JKenneson/Smart-Doorbell/Arduino Testing/Camera_Test/base64_640_480_test.txt

/9j//gAAAAAAAAAAAAAAAAAAAAAAAAAAAAAAAAAAAAA=EgtRBFEEAAAAAAAAAAAAAAAAAAAAAAAAAAAAAAAAAAA=BgYNCQoICw8OEBAPDg8PERMYFRESFxIPDxUdFhcZGhs=HBsQFB4gHhsgGBsbGgEFBQUGBgYMBwcMGhIPEhoaGho=GhoaGhoaGhoaGhoaGhoaGhoaGhoaGhoaGhoaGhoaGho=GhoaGhoaGhoaGhoaGhr//gAAAAAAAAAAAAAAAAAAAAA=IQAAAAAAAAAAAAAAAAAAAAAAAAAAAAAAAAAAAAAAAAA=AwQFBgcICQoLAQAAAAAAAAAAAAAAAAAAAAAAAAAAAAA=BgcICQoLEAAAAAAAAAAAAAAAAAAAAAAAAAAAAAAAAAA=MUEGE1FhByJxFDKBkaEII0KxwRVS0fAkM2JyggkKFhc=GBkaJSYnKCkqNDU2Nzg5OkNERUZHSElKU1RVVldYWVo=Y2RlZmdoaWpzdHV2d3h5eoOEhYaHiImKkpOUlZaXmJk=mqKjpKWmp6ipqrKztLW2t7i5usLDxMXGx8jJytLT1NU=1tfY2drh4uPk5ebn6Onq8fLz9PX29/j5+hEAAAAAAAA=AwQHBQQEAAAAAAAAAAAAAAAAAAAAAAAAAAAAAAAAAAA=QpGhscEJIzNS8BVictEKFiQ04SXxFxgZGiYnKCkqNTY=Nzg5OkNERUZHSElKU1RVVldYWVpjZGVmZ2hpanN0dXY=d3h5eoKDhIWGh4iJipKTlJWWl5iZmqKjpKWmp6ipqrI=s7S1tre4ubrCw8TFxsfIycrS09TV1tfY2dri4+Tl5uc=6Onq8vP09fb3+Pn6/90AAAAAAAAAAAAAAAAAAAAAAAA=+SJWKjGDnNMgR2Y/M2fTNcqske29zQRSBgE1aijIILM=YFZ2tqbRJwrzsAW+Ue9VL7XrfTFKRuzy+i5/U9qaV2k=E1Kipxcmcre6td6jIpkkdEwcIGJWqo3dGJ9+/pXRG0c=RniznzSbFXPGS3T06U5c4AY+1DZFzqvC2jtL/pdyCEE=9wHv0rp55GCn52x2xWM5XkWtDB1S/aEY3Ese2a5Z5XY=Yksxbvk5rWCS6E3uaNjCyL5smSdvAAAAAAAAAAAAAAA=6h0Ei4P3jjHWr9kWLglifSlYLs/Rb9ieCRPgqs1wzPI=z6tctuc7jtBUAZ9OD+dfPXxlu5rz4zeNMzO0cN2sSKU=jhcKM4HQVlNfu4j5nzNnp/7K0kn/AAAAAAAAAAAAAAA=iQAAAAAAAAAAAAAAAAAAAAAAAAAAAAAAAAAAAAAAAAA=RlmlG5jyeprmkkq0tC1J8q1PINVLhm+Y5781zk7sDww=30zXTFaOwmyhKW3E5YZ9DVdWbB5YVd0ok3GNKwHenQI=QPazzS34jnRl8qIxuTIO/IBGf0regoTm41NiJuS+Esw=MpkhyzMCoxz3rOhleSRiScDp71jLROxRYDsOCT/jQHM=/CWx7VHNaV2h2HhiAAAAAAAAAAAAAAAAAAAAAAAAAAA=YRyMYY8e9S/IZajlZscn3Oa07aZgMbmxWbYzdsLthj4=ZsexrrNLvXG352HPrWfkDPRvDepuroPNkHphiOtfW/w=LdcGs+FYUdsz2bmGTJySOqn8Qf0oo3VVWCcrxsdlLEk=PE8Uq7o5FKsPUHg18oeItOu/CfivUtLuJp2RJfMgZpA=nfE3Kn/GrxStyyFSb1R7V8IvFEepaGdNu5ib6zkYBpI=Qs0ysS27JOSckj8q9IrTDTUqduqJqXcm31IZ4RMhDdI=uF8S+HpHDNGzlTXFi6Vpc76mtCbXunjviPR5VLks+fU=ya801iwdC2S3Xrmoha+hcm+5xepwuu7lh+Nee6yjtKw=Mt9M10poybfc5e4DjOC31zWbKrZ6n863TW5LZVaN2bA=CcitC0hMa5O7Hf3psETMXzySc+hqHcwxljUxtsMh3Ns=ScsT70xyRjLE57Zp6XHdLQhaVu24k9801Ac5ckn60+o=2K5BcI/LoxyPQ4oilLrwxznH0p2BseWbAAAAAAAAAAA=aT3BCBmxgMaQu2Op/Ol5CejGhsjPzCkz2JY+hzTHcT4=7/Eee1IHOBwcnFHQV29RNzL8pPPY+tNLMQp+bJ9DigQ=AAAAAAAAAAAAAAAAAAAAAAAAAAAAAAAAAAAAAAAAAAA=MwHbtVyG32EHv0rib6I95K5cjgHBbk9KgvNRtdPGblw=MwH3V5NJXeg51FTV2c5qPiW4utyW37iE8fLyT+lYqjM=ln6scknvXRCPKjx6tV1JXZaBO0dhwAakpMxA9MVreH8=RX1m+VMDyVGXY9MUbFJX1PRzDHbxLFGMIowKzZTwcis=DrcswNQsBM/mA4YdKyrexZZ2MoAQVundE6XLUr+WP5U=Q43DLYwSMcUrdiSaIZI9K0rMAAAAAAAAAAAAAAAAAAA=p8AvC0gxm68+dsepmcfyUV8o/EZhN8V/HjnqNbmTP0M=isJz92EfVjS1Z6p+zXKYvHA2dWh2kd8HNfY9aYbeQT4=hz/jZN/hm+z0VQTx718NePY8XUoI5yaxqL99IafunjE=q6gMxP4VzVwME4xWkdBGfIuOn4VWXrhupNbaNq4nsV4=5yGO326UsNuOGkAx1pgtB89yFXyovvHrimQxhEGRyfw=6mWwKxIB09zQDwAAAAAAAAAAAAAAAAAAAAAAAAAAAAA=MrZIweKbvoO1yzF1/CtC3fJAHX6VnJDRr2kuCK6TTp8=kDPHrWbA7bRb3aVwenevoX4K+KV07X1tLh2+zakohAw=8CXjYT+o/GoT5ZJhL4dD6Orx34++HRNpVj4jtY2NzYw=gguCo4MLngn6MRj/AAAAAAAAAAAAAAAAAAAAAAAAAAA=1cZaCKZWdQcHbnqD2r63iZJIkeFt0bqGVs5yD0Nc2F8=jZdToPqKaFZkKuMg11VYKcGjNOzuedeLfDgKs6ICvsI=vE/EOjFC/wAAAAAAAAAAAAAAAAAAAAAAAAAAAAAAAAA=9K6YsyaOUu7QjPHHfFZT2pbgA/hWyJFh0/awZh+lTPE=BQMU79R2Kzr0yOlQyJ3/AAAAAAAAAAAAAAAAAAAAAAA=LSEMYQdB+VIV4Jxx0oirBuhjAAAAAAAAAAAAAAAAAAA=JgQwBFJjkH+lK73YxOnWkwScClfuK3UQjjikwD0HFAA=m0EAAAAAAAAAAAAAAAAAAAAAAAAAAAAAAAAAAAAAAAA=dcCmZ5yMVSKVxDj3pOo60BfU/9H5bitmAyeQBxUNzqk=aWJ+dtzgYAUZzXDGLbsj3J1Y01dnP6h4jubglbf9zH0=9vU1jMQxJfkk5P1rojDlR5VatKo7jguT+NTrGRngdP0=abZkmSgYC7gOBSgDpgdanXcRYtLKa+uFt7dS0kh2jAw=816/pWgx6HYJDH/riuZT75zisqkmvdNI7EdyvBGO9Y8=OMDmoQ7mbMPmNUJmCcEZNbRvbQmxnvlyDnjPJ9KdGOM=jGM0+hN9LFiIeuPbNaNuMQPjHQ4pfZKR+o/7NVr9j+A=X4JixjFiWx9ZHP8AAAAAAAAAAAAAAAAAAAAAAAAAAAA=1hWj78PR/oC3Z7h+zBZifxldz4BEFoWz9eP619bVthk=bhU3RkeKF3eH78HvGP5ivhz4hxYu5uOcmsK2lYcfhPE=LWF+d8iuXuV9uDVx1HsZ8vfOM9gBVXoxzjFbrYlifZw=uwODt9qZcSGFDhQWA4FEXuIrW8LZ8yTqatHkemKmS1s=gNBPGe1OznjaKuMewMkCjAIAAAAAAAAAAAAAAAAAAAA=LDParMYwvHNUMnjJBq5GcHGfpWT3GmaVs/vz71uWMuA=gD8qiwHWaZdbCOn4V6LoGoumxoXKyIQ0ZBxggjFYzTs=aDR9qeF9fh8T6DZapb4Hnp+8QfwOOGH5g/hireq6Xa4=t6bdadqMfmWt1GY5Fzg4Pp6HvXfD3qS9DJ6PQ+PH0y4=dG1K90vUQPtFnM0DHsQDgH6EV9N/C3WTq3hK2jmObiw=T9nkBOTgfdP5Y/KuKhJxqpM0nsdpRXpGRUv7RLqFkYc=XpXj3i/QCjSfLxnpXkYmHJVv3N6TurHjuuaZ5cjfLn8=CvOtX0VZCzR457GrgNq5xt5oYVm3FQPrWNPpscJIAAA=da0u9hIz5ocdPwxVGWPHIFUthFR0IA45z6VXkAAAAAA=pK4NlRgX4XgeuKQR7elX0JGsvBqIjHBHSnFjQ0jHTmo=OVN6lWAppAyohMb7GB9AanIPbpS5ddSb2GEc8Y+lAUg=yR6cUpPuUg56nFN5pWF1A8GkwFPAwT1wKfUdxpHXHHY=6UgXHp+VBBGRliAKQg5PTI7VXkWmNKnApMemOD1p2DQ=sf/S+PdS1G4kQ4YqCOgNc/Ixx0681kkkbVKjm7sYDkA=J9KOpGO9UmzIsRowAAAAAAAAAAAAAAAAAAAAAAAAAAA=vawj1r4feFPsFkNVvo8XM3ESnqo9a6e5jwAAAAAAAAA=pmy7GLcRnHTp1rGuhgnjiiNxaGTNxknmsiZizdOK2TI=bkB3ZGBx65p67j1H0p9CSxCC3BHHStBRttZCAAAAAAA=Vi1a5+r3wTtDY/CTwZCe2lQt/wAAAAAAAAAAAAAAAAA=6mbUZ2zjr85qau8H5f5C6s+k/wAAAAAAAAAAAAAAAAA=hX1LWuH+F+oVN0ZniNd2h3w/6Z/1r4j+IsZF1N6BjXM=4j+N8gj8J4VrQO9jXK3PJJxVR7DuUJenFUX+8PftW60=VcVyRLuRVCLjbnpULDcckZohZLUVw9hijBPTtSba9Bo=FGCQMUAZBPr701zJCbHZ+XnjH6Uoy/pimNjouNy5qeM=OD2xU69g5tCwjfj6VaRj3qGuoXsXYHIwK17WUgioe5Q=dJp1xgZB4rtNEvCjKc45qGB9M/AHxUFnvPD1xIuyfN0=WoPUtgAAAAAAAAAAAAAAAAAAAAAAAAAAAAAAAAAAAAA=W+BHc4tLsAfx4JRj+AI9to9ai+E2t/2ZrP2eRsW9+BE=uD0Dj7p/p+NcU3yVX5M33gj3iivVOcDzXOeJdLW7t2Y=C/MBzXFjY3gpdjSm7SPDfFGjiMvxXlOtaeVZuO/SuSk=yNZHEahaYySK5u8t+ehrZslGNcxEZ4HFZksZA45q72A=M+XEedx/CqTqXOW4HoKtaLQQxkAAAAAAAAAAAAAAAAA=qRxmoWUjrirTBNDT6ED8Kb9cdKa0YMrXMRkTgDIqO3k=WZSrHkU2rIW6JcZGAaaV4qE2lZoLhz14o780PqIYc5E=zxSHJ6Y/GgbQjg7SAAAAAAAAAAAAAAAAAAAAAAAAAAA=AAAAAAAAAAAAAAAAAAAAAAAAAAAAAAAAAAAAAAAAAAA=9KzSSWxyAAAAAAAAAAAAAAAAAAAAAAAAAAAAAAAAAAA=TkUKTnGfpU3urWBPUcBnvXb/AAAAAAAAAAAAAAAAAAA=rQ5Y/wAAAAAAAAAAAAAAAAAAAAAAAAAAAAAAAAAAAAA=2c9K4k9bl7MybuLHTHBrn7tfmz2I71otRdTnr5wTtU8=1rJbg89RW60XmQ0iIAAAAAAAAAAAAAAAAAAAAAAAAAA=WgQfsVx67DjHNE3psUrH66fD5BbfD/wqj4URaNag+2I=Fc1+cmnMZGnk4G+5lbj3cms6v2fQSd22fUP7Kigar4g=SOn2dB/49X09WtD4X6kz3KGtp5mkXig4zEa+KfiUv+k=U+em41zYj+P8i4fCeC62Pnb1rkboHceKuDQWM6TPJGM=8qpS43Y7d62voLQQr0GBx3pMAkDjmndtaAmmIPUEf1o=XHTGMmht7BdAPw/wpc4Ix0+lP3nYQffx2HSnjGcYHak=oPIF+WTnoamWlvqUrJFhDwM1ZjIY8469KiWmxLLcJwQ=HrWlauRzxx3qHuVob1nNtx06V1Wm3Owrjk1m9wPUPAc=rkuiaxYarAf39pKGAzwVPDg+xUkV9sWtzHe2sFzbtug=Z41kjPqpGR+hq8M7TkiZ7IyvFuhjxJ4a1LSz964hIj4=cfOOV/UCvm3SJJLWYq4KzQvtbPBVx/8AAAAAAAAAAAA=/dPpjw7qq6zo9rdg/OV2yezjrWpXZSlzQTMXoFMljEg=hBHWnUjzQaBHl/jLRBuYqvHrivFPEOmbC+F5rx4NnW8=VHnGq2eC2Frk72A5PHWuiLZm0c/dW+0Hisa6AXORWi0=rCb6mY8Jc7n/AAAAAAAAAAAAAAAAAAAAAAAAAAAAAAA=omRsMZJqMrnkD6ii9kBGy+uKjbI4/rVoNHqIy5HOBVM=ni2OGQZPfFFwJVcSIMdfpQeoyP0od9xITFJjAqZPyDQ=EI9MEUgHHApeo2NB6ZXt6U1kzz27e1NO2gtFqIF+Ue4=RmmkbF+bGR+tUmF9SFiXJwMUqxZ+YjJxTuCP/9T4iuc=eGwc4quSB1z6VOyGwVd2CenrjrVhBwoAAAAAAAAAAAA=yOD04p47f07UnJ9BF/RtHuNd1KCws0LPKwAAAAAAAAA=jYWVpoGlW+m2IVY4gN5H8TdzWNd9DSOiuVpZw74Bzmg=ZMqcVy+g0Zt5BkNjp24rlNVxECB1JxWkXsJnJ3OMkDo=45rPPfHU10X01Exq5J6EDtUqgZApp6i2LKDGO9aYQPY=zjHUgfrUVG+UI7n63W5bT/h7ER8rW+igj2Kw/wAAAAA=k0chraNv7xJ+uTU1fshE+pf2VFzqHiNu4hjB/M19N1o=Yf4H6iluVdSXdp12P+mLfyr4q+JqYvJxyRk1y4j+Pbw=i4fCeBa0P3jHHeuRucE/hjFaR2uBmTHsOuaqTYUrkYA=T6VvEQ0gHGQfbimnpjjrVJ+QkKPl6c/h1pOuOevHFTw=+t7AhM9D2zSct9Kq7Bkq4AAAAAAAAAAAAAAAAAAAAAA=644z09aL30GtydOgP5VMh5HGe1Q9QLMTc4weKvwtjqY=pegI2LWbaeOfSuo0yT7rMeazlsM77w/PhlUnjoRX138=BzxANV8LrYStm400+Wf9pGyVP8x+AqabtVQSWh6JXgE=8U9EGheLku7dStrqimY8cecD84H14b/gVb4qLcE10Jo=b1sdX8Ldb8u4l06VsJON8YPTeOv5ivVKWEleDXYJrUI=iuogx9c08Xds3GWHSvD/AAAAAAAAAAAAAAAAAAAAAAA=J5JrVkUZiF4ridStsbsjpW0XcTOWvkIyEGTWJNaHO50=Ru68irvoIzp4+px+VZ8qnJJ6Zq0xdSo6+1QkcHFXuLw=yuQDnnt3ph4GOc+9PURG4B5xz1qLvnGatB0EHfH50xw=BhjAprcOhR2m3kJ6qe/pVgHIz1ov0Q9NxOvTvSfnU60=tSRpxnpzSUXGIwz04pCuCDyeMdKVxNkbYT7vHrUBJkM=znb71aGS7VXAGfqaO3ynIpID/9X4lurlZyeMZqjsLH4=bPB4qblM39D8Lalren6hfadCWstOTfczMQFQY9TWWCo=QGBymMg+tSwRMrbm5XAxn608DPYk+g70rW0Cx7v8OPA=svhzR/tl2o/tK7UN05Rf/r1raoWYHy2OTXJOXNI12Zk=1m9wsv7wHHrXQRZdQDwaliG3NsBGSa4PXIyrMWzntVQ=AZxd1w+c1SAByeM10shihc809eMfWl1DoW48Z4PXrWo=26blgHczxr9csBU1H7o47n62eMwLHwAAAAAAAAAAAAA=YW/wr83dDJGn2mc52Anioqy+FeQon1V+ylk3/iMj7vk=UYJ9819N1th/gfqKe5Xv+LC6/wAAAAAAAAAAAAAAAAA=kn7xrlr/AAAAAAAAAAAAAAAAAAAAAAAAAAAAAAAAAAA=bIHqB61ugEIwByT9Kjx+FVqToGM84Pr1o7VHw7jfkNI=OeacM44/SmnoIcGxnPUGnjpnn8aL3YbICNynBzxToWw=jn6VQ+pYB568Cpl7+lQw6liM9AOKuQPjAxn2qNbXDc0=W0OMFjyTXS6c+CPT1/Kpeo7Hb6NNtZea9++EOv8AAAA=v2xdwILsC3myeME/KfwOPwrFvlkmO10fStcX8UPD39s=3hWd4Fzd2H+kw4HJ2j5gPqM/iBXbWjzU2jODtJHjXh0=1SS0mguLckSIQ64/lX0fp19HqVjb3cLArKgbjse4rkw=I7Ta7l1ehaor0DIZIgdSDXnHjHRtxdgMDrmvNxkbTUg=2ovdHiHiLTfLZ8jivNNWgLMyxg981nBls5a7tPLJ67o=sK7ix25rVdiepj3EdZkydjz9T1qlsJlGRODgniqzDPQ=rRbAQMuecHce1QsOTxTQkM28+1RHoMirTuK4w03bg9Q=+9NXsDRDLFvUgD8KrQ5j+VqE7ICfg55prD+VJu7GhMc=QfhzSEetTdh1E7VFJJt+UHtzTJtrYhCNJzggCptm0DY=jr61TY9gVdx7jHWkwDtIUcfrRcN3qf/W+F2YdOp9KFQ=dtkcClppWCoPUmgpH0R8T5LX4VfCLQPhxo0yNruuqL8=1yRTl44TyqHHTccdew968HjjVVXaMAAAAAAAAAAAAAA=nA4/lXb/AAAAAAAAAAAAAAAAAAAAAAAAAAAAAAAAAAA=+S73Hk444wK7r4H+AAAAAAAAAAAAAAAAAAAAAAAAAAA=M9CTz9Aa5Urlp2d2eceLZU0T4keMNJ05M2Gl6tLZQA8=cRnaf1BrQspDPCsrROoPTiphJTpxmuquG51egeFrjVs=R7vVZFP2OE7VPqa8m8YKIp3A7HjFaQavYTTPPbrqSe0=VTHtXTfQhDlPTinoOf8AAAAAAAAAAAAAAAAAAAAAAAA=3XkPP/AxU1NrFR0aP1W+LF2tj8MfGM7dtGuVHPdomUc=6mvzq0rK2lsp4IjX+Vc9ZWrP0X6ijsfVn7JpDP4n9R4=UOP+BV9MV04f4H6kz3K9/wAAAAAAAAAAAAAAAAAAAAA=/TqcVyYi/t/kXD4TwLWzh2HXNclcdc4x61pB21Bma4w=Hqc9OmapzD5DjrW8RaDVwQOc4FNKjvz0xVdRbCZGeMY=BTDz9KNBihQRyevSgjJHFF09BDuSfen57UkwHDkDjjE=SRjBYZ79BTHuTrg8c+vFTJ0/nUsL6kyNjgfe7GrkGAc=nkk5zUvYXU1bZhleePpXQ2D425PFZXK6WOu0iY5XmvQ=/wAAAAAAAAAAAAAAAAAAAAAAAAAAAAAAAAAAAAAAAAA=z0ccN/j+NbIrtpvmppmT0Z81eJNIPhjxVf6coPkBhNY=5xjKNyB+HSvUPhhrQkim0yQ+s0WffqP6158HyVl9xtI=1hdnotFeoYBWPr1ktxaOWH3RXLi43p37FwdpI8F8Vac=PPLII1xGDgnFeZ6tp4j3BFFcMGdDOI1G3xniuau4euQ=VutTN6GHdR+o5NZM0fOd3NWtw6GfKpxwDmqbpj8KpMQ=QuhIOe9QPySDj2qgVmRdajcL0br6VZPUi/yaTr3qh20=Rp+tVLiL+IfeFCQn3EgfzBgn5hxT8c80mlcBMZ70hGI=k7XDZkUkoXpyf5UxIw3zyUbIG+pNtA6DoKavDHHfmkg=LoUnHb60wHIbg5P86fQSP//X+FkAAAAAAAAAAAAAAAA=FeNsqfQipbZSLd9fT6tfTX1/K893KQZJHOWOMAAAAAA=jCnB446+tTa+gN3Zf07T31K8jtoyQXIyR2Fe0WAh0mw=obS0AAAAAAAAAAAAAAAAAAAAAAAAAAAAAAAAAAAAAAA=WX0/lW97fESM44SK2T73/j7flSpL3rMJyXK2fHGlTy4=uXV9qt4S0+p3s15IW5JMjlufzr2z4VXOoeMNa07wMlk=29zpu7dO8keWjXGWO4c9OetY8vJBQXQcW3qfTHxN8LY=keC/hbNZ6HarBDFIMHqWJB5J/wAAAAAAAAAAAAAAAAA=Nqkoi5r6nAzkn3zUB6+9dT3ErBj1qZQM5xx60tQuWIU=fmGcVu6K4j1bSJD91b+AsP8AAAAAAAAAAAAAAAAAAAA=BbxGuSJtQWOyhwOrO4zn/gIavhe0BQRoTkoAAAAAAAA=diY7H1T+yS4MniZRzxFn9a+nK2w6tF+opblHWZfJ0m8=H9Ij+tfE/wAAAAAAAAAAAAAAAAAAAAAAAAAAAAAAAAA=Vyl0ASRVxGZjg9e/c5qrLyDWqFoQr90YppUnHcZqrMU=ewzl8kfd7UvoAAAAAAAAAAAAAAAAAAAAAAAAAAAAAAA=DD6U4H0B5q7O2hNh6kkcUg4kBwRnvRfQZMD0I6ipFYk=PbP0oAnj4IzV2E+vWs27IZo274OO1bmny8j1qGB1WmQ=3zKfSvQPD10VZBms5bDPpb4Oa6We40yRsJInmxAn+Ic=3gPw5/CvXa6MK26dn0M5/EeX/GfRBLpdprcEZM9lIIo=Ygf8smPU/Rsf99GuA8May+l31tdR8mJwcZ6juPyrlxA=nGo2awd42PouCeO6gjmhbdHIoZT7GpK9GL5opmD0CoY=5gW4jZH+6RzUVoc8HEadnc888W6KiK3lrgHpxXiXiDQ=4o7/AAAAAAAAAAAAAAAAAAAAAAAAAAAAAAAAAAAAAAA=/dxZyew6YrFnhGP1qlfcNzNlTGR2qk6g9OnvWmpN7lQ=YZ/+vULqOuP/AAAAAAAAAAAAAAAAAAAAAAAAAAAAAAA=I8HB9aauVcQjp70wrkYNF7CKTjyJQy/d9qmQhxkdKls=dg8wNQvIW+VPzo1YvUI4QDufJOc4p5UMCOcU9R9ROc8=HajB9Bj2pMQMCRwSD2pu3AJzg9zTuI//0PhlVxjjn2o=lUcf40mUTISTn160qA57nOP6YqNAseh+GLFdMtvPlUc=nyrj1IFbTXpPHr6muebTloaJWRFNqH2eKWV+AilutfY=/ZrL8Mv2JrqWaFVu5tAkZ+cZa8cqrcd9syn8BUyTcJI=W9mFtPmfJfhyy+z2ltCOscaivrf9kTwmIbHXfE9xEPM=Lqb7NAxHRV5b/wAAAAAAAAAAAAAAAAAAAAAAAAAAAAA=AQf8a/OjxXJ5l5JgE80f8vpP+tiFscVOD096hxnPPbo=10OTQCZPGMZ96mjzjk/lRbuOxbhGTzWtYQSXNzY29ug=WnnuY44gOu4sAAAAAAAAAAAAAAAAAAAAAAAAAAAAAAA=ZTIersrLGT+O8mviq3DAqW6kZP1rKorMiGx9SfsjfLc=PihT12xH9TX1DWuGvyainuYviyYQeHr92/uADHfmvio=8d7pbqVj6nFc1XWuy4/CeNayo3NXJ3ScsQAAAAAAAAA=ciqsvuDn17VsiCqvCkDsaa7HkDI96q4BuxnHT0xRvxk=yPpijdB10Gcjk05k2gHPBp27hcTAPT1p456jFD8h9Bw=G7Y4FJJggcYxS2AkDemKmjIyCTzSYrlhSO9WYicAAAA=0NMvQscgtitqzlwVPvSvoPqdNp8vTNdpotzgrzWXTUU=1PYfA+uNp97a3UeC0Dh8HoQOo/Kvqe3nS6ginhOY5UA=6n2IzV4Z2k4hPZMg1TTodX027sLoAxXMTRtxnGR1/Do=18wCObSNTubC6AWe0nMTgex6/Q0sVH3kx09j3H4aa4I=+06SwkYmS3+dM/3D/wAAAAAAAAAAAAAAAAAAAAAAAAA=F1btxyK8R8U6XteQ7ec141SPJVaOmm7wPKtZsdrNwK4=H1G35IxWsNRM5i8h2Zz2rDuYdvQAAAAAAAAAAAAAAAA=fKhyeMVaYWVym646dKgIz1z9KtO+oMhYYyO30qLGeo4=avqTuRMMgZ/AYqM800x6NDSQKb09KatsIgkUOuDySPo=VVV/Iba/SjS4Nj23P0Py44p6xqg4GfelcEKBR69PzqY=7ExOcDI+tNOSPlxTbHa4hbjuRjNNLYAx2GcZoQtbH/8=0fhxVH4dqeOOcdqllDgMjArd0CwWecSzjEaHIGOpqWs=S5R1r3PvnHpVC4vWRsBjnucViorZg2M8+XUXtdPhHmM=31xHbqFHJLMB/Wvv79sS6h8O/CPwp4Rs5XH23Ura2Vc=oHgt0JbP4iOnJKMW15Ib6HzLpMQMbNjnB6V+gHwV0Nc=w/8AAAAAAAAAAAAAAAAAAAAAAAAAAAAAAAAAAAAAAAA=mxUkHDytj0OB/SvgjXpA07Y5BPFTH3qjfmStjlZ/v5M=1qDOWxj8q6OQAAAAAAAAAAAAAAAAAAAAAAAAAAAAAAA=Kah8WPAdtOu+KTWoA6noVDZP8hWUkWnZn6CftLgH4G8=jAHvBEOP+u8dfC8ERwnfgVNb+IRHY+mf2SwI9U8SIOg=0EZ/X/69fUtXh3o0E9zG8U2pvNEuU67Rur478fWvlTw=ox3NclRNV2XH4Tw/W0AY8ZrjrxcMffvWsdRdDKmABz0=jVWTByPWtdQsU8AswGeeuKUjHv25rS3QVhuDggde9Rk=x3J604qyCwh/e/IpOD3B5qZyAioOcd6LaiGfdPA4Bpc=v+NLlD0HDrSMSxKr+tCjZWH1HxgYx6cVMmTihjWmxOs=2x0qzHkfTFR1sJW6l2FuR+datrIMjB6Vm4jsdDp8gBU=ArrdKnIIOajUND0jw3fbHQbuK+o/hhrA1DQfsrsTLZs=BRnupGR/Wik0qqCWx21eFfGjQ/sHiCy1qHPl6gnkzeg=HQAAAAAAAAAAAAAAAAAAAAAAAAAAAAAAAAAAAAAAAAA=j8ua+jVZXVWQgqwyCO4rPCvVxCpvcWiuwgZIoZSDXnM=4u0cHeyjr1rzMarTT7m1F7o8U1/Ttrthelec6ra4Ykc=Sog7Fs5G/gwTwa5+6iGcVqlcnqYdwhycjkVnTqOcnio=1oIounPIPoKqkVaB6kTDHAGcYPSoCo696vpckjfjoM4=TURXjrmmNDT+mKYenHemBDJIEHP61VkiaQbuM9zStZ0=0K9h8BBQDow61KR3od0NaDRxwaABRbsJiEAAAAAAAAA=DBBHHpilYNBCNxKjoMcUm3jr0HUHpTQXSP/S+HQuSOY=nAdxip3LV7Fi2gaeZEQAAAAAAAAAAAAAAAAAAAAAAAA=uQi4LfQVWa5VxhuaTQWPSf2efD7eIvj18PbKJEYRaiY=+kDDjZAhkOf++a+kP209Ye++I3gvQTt8qw02bUOn8Uo=/l8/9+uPxrObSjZ9dvzHdqyPL/C9l9tube1AyZ5FQcc=vX6P6Za/YdMsrU4/cQJHx/sqB/SlR+NhN+6j5S/an1I=ZtfNuzZENuoTPbIyf518V6uRJO/1rOk/efqIwJAM8+k=UIHrXTfXcbT3FCj8anRc4zVXsibFyBF3D0r1v4BW4m8=jL4EDdV1MP09FJ/wrKd2VfRn3J+07N5XwW8Qpx++aCM=5/67If6V8SxJgqv4ZqKyftCY7H0V+y/cC117U1Y4WRE=U/H/AAAAAAAAAAAAAAAAAAAAAAAAAAAAAAAAAAAAAAA=1MMc7jWVf+P8hw+E8A15PnY+9cTdqOcnnpmtExGRMMk=9qpSYJOD9a1SY0yuBtZu2aCPUjA74qxMYUHHP1pmOmc=jNAeo5VSNfkOfwoPJ56HvUuWu49QOMflQAO5qk31JEM=zlVx7mpVXaMDrQNXBMB2B71KOvv0oGToemOmKmjySOY=psIuxMARz0rRgI4CnvWctxpm/ZSdMV0+nzcgg1m2B3M=ol1sKkN1r3n4V6/9h1i38x8RXAEMmTgYPQn8axb5ZJo=KtdH0BXNeP8AAAAAAAAAAAAAAAAAAAAAAAAAAAAAAAA=Cr0akeaDSMYuzufNOkTHCO4+dlG7tz3r6P8AAAAAAAA=gRxzODc2p8txnkr/AAAAAAAAAAAAAAAAAAAAAAAAAAA=uWQubZsjoDXHjYXp3Lpu0keKeJ9L8tnO3pXk2t2YUtw=VxUzeRxGo23Xjv0rmbyHBPSuhMzZz91FgEcen0rKmQA=zVq4XM+ZTyeKqSDr69s1aEyu6jvwKhYDHvTuw6kRA9s=NRMOucdcYrRbghjAEVBK4HA5NO4tiIR7jl+TTtnPBo4=lhFSRTBLkEYqwGDLkc+mKb0Y730AAAAAAAAAAAAAAAA=vU63FqxgXjG4nvTSoLZ4x3ouNan/0/h73Gfwp4A4GD0=aizLN/S7cQJ5rD7w44q3JKMZbIrP3rjuZ89xuds546U=Pt8SODzgVVnYm7PqP9hPQY9X+NOtarOjMNE0bMJxwks=KwT/AAAAAAAAAAAAAAAAAAAAAAAAAAAAAAAAAAAAAAA=IW/WsakbxTfR/pYpyu0vI6L4O6Uup+NdDtpB+7a6UnE=6A5r7470Yf7TCeyPg79o/Vzd+NNYwxKpJsQ5yMLxXy4=ag26RuTg96yw+12DZjucsOv5daYQeOK6rO9wHDqMg+0=xiplOMY70KMg6l23TnA5I617d+zTbi5+OHg1MH5JJ5M=8oXP9Kzm2V0Z9hftUtt+EN6P717bj/x+vjiIZkpVvjI=I7H0T+zDarc6/qbuMi3iVgPfpn9a+p6eHWsmOp0EZd4=Cp7jFfJHxUhxe3BH945rLEL96mOGzPnfXlwz+ma4a9E=luOKqImYswycLnpVRgOlaq7QeZWf/Wccg0YyO4watXs=AAAAAAAAAAAAAAAAAAAAAAAAAAAAAAAAAAAAAAAAAAA=4o68HJpuSxwvShp7MXUcoA4wakHrQk+oIRvvg1MCMYw=02UiVD2/UVPG2OKl3DctRMeOOtaEDckAAAAAAAAAAAA=x65710mnzdMGspbFXOw0q4xtOTXpnhvUWUqFbDY4Poc=tWUkxp6n1X4V1uLxBodteRNucDy5c9Q68H/H8a2a9Ck=vmpoxe58yfEDQv8AAAAAAAAAAAAAAAAAAAAAAAAAAAA=gj6V0Xw018abrsAnk229yphkJ9Typ/OvMbdOW2zNpe8=LQ95or1zAAAAAAAAAAAAAAAAAAAAAAAAAAAAAAAAAAA=u4la8eGmh1vVHnWq2uGbqOa5C+gwW6/TFdS2sZvc5y8=Icbh2rGnjIDccfSrVxdDOlHHQ/hVORc8dCD3FWtBFV0=eSDzUDfXNVqxdSFh65qOTHbg/Sr6jK7yZ4QY96akQX4=Y9aNQTDABHXA9qQrkemaFzK5LIpoww2n86q27lHKOOM=tgd6av1As4z26Uh7+lQ2x2DJA6c9qafx/KhdwCmYCHk=zwOOKauxH//U+HxxgD171esrcyyBmHyg8moZVzZMgRQ=YwRVO4uCchTWcVdjKyszPhsE/Sr1uQvH5cVclZAfdv8=AAAAAAAAAAAAAAAAAAAAAAAAAAAAAAAAAAAAAAAAAAA=tt4o8R+IdfdNr6zrFzeEL0G+Q4A9scVyzi04yXn+aKc=ZSt6fkfSf7NWlfbfGsEzKTHaQtKT6HGBX2FNKsEMk0k=9yNSx+gGauk7RlJkz6H5rfFfUWvdc1CZmLeZMx6+9eI=t78zHr61FHZIb2Mp+vTgn86b0yB26e1dUXfQWg8fw48=1qZAOOaVmtgReteGGfy9697/AAAAAAAAAAAAAAAAAAA=hhWbWqQ76H1T+1jJs+FGP7+qW6/+hH+lfIcH+sAqa3w=Yo7H0v8AAAAAAAAAAAAAAAAAAAAAAAAAAAAAAAAAAAA=T4rxj7ZcYHG41hif4iHDZnzf4gGC57VwV/zkL604vQY=9zHlG3iqjjA46itUwt0Kkn3x39TRwOlVYRGRg5/GmqA=EYNV00ExBwAAAAAAAAAAAAAAAAAAAAAAAAAAAAAAAAA=k9NAuOGQQM/SnA8DpVLYEJJnbkdqfGcgUWH1LEftUqc=HbrU9RJlqPgDNXbd+RzWctSjTtZPmGeg5roLKXkY4z0=amXYfQ6nTrkowyeK7PRL55XRImIGeWrJrQAAAAAAAAA=/aNLzhZV89Mnq/Rse5HP4V67XVhpXhYzn8R5h8bdBa8=vD0Gr26Fp9LkzJgcmJuG/I4+nJrxnTLsowAAAAAAAAA=JiV+8ZpD4T6a8I6z/bugWl0zbpgvlzf74HP9D+Nbdd8=Sd6aZk9worQRha/ZC5t246V4l4n07G/jnPNeJJctRo4=mDvA8p1qzILY5rhtSg+ZsetdEdhHMXsfBPWsK5TB+vs=VcdiTMmUc+1UJV7CrAqyDGMVAyc9BV9LiK7EAAAAAAA=YmVjjIGatAxyRBQexFNx70Ju4Jobimc9jTe4hpAx2Jw=1UuIyPnXgjrQC1HRPvUZ6ipD7Cm03sICMH0NMI561Ho=hewmMd/c+9BI9cH6U7g+x//V+Io0LMFUZyelbUCLBEE=FyWxkn8qzexY2WRVXIxmqO4nr1NJbXE9yxAm0bmNTh8=by33V5zjoactwWp9/wAAAAAAAAAAAAAAAAAAAAAAAAA=blHKzTO8MWPxEfPvXy54WhaCws42+8sa7hjvXJKU3Kw=1pb/AAAAAAAAAAAAAAAAAAAAAAAAAAAAAAAAAAAAAAA=T4N1q7XG5LVgM+/H9apf7vL5il8SPzR8bTebcSnuxLU=eaXbZYgE/wAAAAAAAAAAAAAAAAAAAAAAAAAAAAAAAAA=emRU8KgMMjpVNvUfmaFp8zZxj6ivoD9k+Pd8cdBP9yw=rr/0Uai/vIFsfTX7XDY+F9kOMtrdsOme0lfJcAIcc1M=Vd52COx9Nfsrj/SfEh7hIe31r6TrTD/C/Ume4DrXy38=FlNt7cZ7MayxPxxHDqfNPiIEu4B+tcJfJtyPT9amPYo=ZizALuPXpVNufatugvMqzjoT0B7U3OBx/KmlqG4mMjE=+lNC8Y5x2pt9LBsNAwAAAAAAAAAAAAAAAAAAAAAAAAA=lUBeaV9dh2shQQAAAAAAAAAAAAAAAAAAAAAAAAAAAAA=GMcU1qrhYmXgDnk4GKnQY288gD8KTBK7LEZOcnn8Ktw=P14JqHsUrGjbtnHA49q2bWYIQS1ZvUDoLGVpiOyV22g=kwi2BeBWbWg1uev+CNdfS760uo25hcNjsR0IP4V9SRQ=qTxRyxHKSKGU+oPIrTCu0pRJqdCO9s4tRsrmzugTBcw=TRSAHGVYEH9DXyHNaT6Hqd5p11/rrGZoW99pwD9CMU8=FLZhT6nrvwj19YNRfTZXxHdpujHbzF5/DI/pXs1XhZU=4tdhTVmFFdJBDcRiSNlPQivKfF2nhGkwP0rysXG1W5s=0Xo0eMeIbLazcYrzzVLfDOCKIPQqSOUvoMZ4rnrqE88=bn0raLIsZNxH1/WqEsXUY+lMRSdP5VTlwmeMk9M1onc=Ap7GlJLggelO2ALgj68Vd1cBjKONp74qNlwOBn3FCEM=CMDPb6U0gECn5jsmhjDj39cVGVH50m23ZE7MptmCQ/0=01ZHODT3s0PQXAAAAAAAAAAAAAAAAAAAAAAAAAAAAAA=D1P/1vi+ygwPNcH2q0zYGT0rK5VynJJlvmPtSRLvYsQ=/KD6UnbewXJ5H3EDoBRcvtsLhh18sjNO2g1sfa/xa1Y=utB/ZH+FfhG2jMEWviBL0MMExRHzio/3n2HPoPevF9I=Rhww+orlcpSun/WhT/iSt3PvH9muxNr4NuZT/wAAAAA=0B/xrS/aA1M2fgY2se4SXcwGQey8n+Yoaf1d+oT+M/M=48XTZupMnua8/uicnHrWlO2wmUWwfXNN9cg1aaejAeA=Hjd2qzGcex96d7gjQtMHjjNfQ37JKeZ8bNNPB8vTrg8=5of8az+0vUa2Po/9rrH/AAAAAAAAAAAAAAAAAAAAAAA=x361nN/vJf10FHY+m/2WD/pficZ/gh/9mr6Srow/wfM=JnuKOtfMPxdQ/b7nj+I8Vjivjj8yobM+aPEChXft7+8=XA34GW561MdhmJMvHA/KqTjgitk7qwbFSc/I2Rj2NNA=RsHXkVXUBpI5wTzxSBgAAAAAAAAAAAAAAAAAAAAAAAA=kU1Zg9hQcYwKXOOg4zmlKauFhQRxg07dyR3p2urMWuw=O68imqcSEY5PNCd0NXLKnp6f1qRWz7GkCLKEAAAAAAA=bb+NZsauy5HIBgse3WtG0YuwLZC9hUvsB1GnzBcCur0=LuMFcd/WpaGmeh+H77Y6ZPT1r6j+Getf2p4eW3kbM1k=Hy+TyVPKn+n4VNF2qoUl7tzs6+fvjzov2DxBp2tQoBE=X8JgnKg/6xPusfqpA/4DXTiYpwu+hMHrY4zQdVksriE=uIGKywMHQg9xX1RpOox6tplpfQkbLiJX47EjkfgeKxw=K7TaKqdC5RXcZCEZFch4tsBLCzgc4Oa8/Hx0TNaL948=D/EllhmyOK8w1q3AL4Fc8DWRxWoQ8txn+lc9dx4zmtg=i+piXC4zx1rMmA565HeriD3M+4kCkhBkmqXkE/NJkms=RWRO4jJkHHX61CR6mqvoBG/Q44zTGzzgf1p2Vha3Ijw=+4pvarQ0MY8YFMIx6Z9fWk+63JZDPGJFJHXtUNvIc7U=6hXtqN7XLHPboaRs9v1oTSBiZ700nHQZNHUVz//X+PQ=p5Yxt4HFVyScjnJ7HrWSRpoQMgPGRzTs7Rgfzq0Gwq8=3uec+1b3hbw3J4y8WeGvDNudr61qcNpnHQMwzSkhw3Q=mfbX7bjWsF98MPD2nKscdkt1P5CdI4lSOOP8OGH4V4E=aLbb5UB7t/WuecUpMUJNrU/Qf4FwiD4fWq4wTMxP5Cs=lv2jpNmlWI3Y4bAzWdR/uo27jl8bPgfxTJ/pEvrnFcQ=XB+b3IrWktLhcqNwB7Unse561slfckkUA47j3qeLOe8=ik0M0LXhlwM5r6R/ZAi3fGKJu8emTfqBWdveRR79+10=yY8B6FH/AAAAAAAAAAAAAAAAAAAAAAAAAAAAAAAAAAA=skDUvEoz1hhP6mvpat8P8HzJluA6183/AAAAAAAAAAA=csdx9TWOK+OJVPqfMHiP78hArz3UOpweKURswpm2lsc=4VScHn1FbJdRtlaTlW7moUPyA56mtEkSxe2WHTnOKjI=C+eDtHtQtHcAAAAAAAAAAAAAAAAAAAAAAAAAAAAAAAA=nqKuc5I/+tTk6ZxzTshtsepFMY4Kt6HmlYLlhDng9CY=pV5JPFSxuxMuScA1YEgQLu61D3C9izb8tucZx+la1sw=AevPrSkg8zds5TlccCum0+bG2s2NnbaLd4Zefxr3X4U=HiFbDXYI5mxBdqYXJPAJwV/Xism+WSY7XVj6Brivizo=D/b/AAAAAAAAAAAAAAAAAAAAAAAAAAAAAAAAAAAAAAA=kj5e0695Rx/EAa+hPg1r/wAAAAAAAAAAAAAAAAAAAAA=OPzNcVJ2qJmkttT1KivRMQrN1a3E1swx0rlxkb0rlQc=aSPFPFFjhpOP0ryXW7Xl8iuCnsdMtzhNSg254rmLyPo=gDiulPQzZh3aBTz271g3JMjFIxx3q0gZVMAUZwS1QyI=kjNMRWYYJOOtV3UrVg9yNgRjPeoiNxOOvrVXuJMi4x4=/wAAAAAAAAAAAAAAAAAAAAAAAAAAAAAAAAAAAAAAAAA=U9BE0Um5eeo4p3NJRSE3cTkZoFRYdz//0Pj+Vm7Dr6g=qIjLZGeOKzRTIGON2B8v0qM4PNPQZJEDuAAAAAAAAAA=laKmt/tGeDo7iMyQWCXN6ec4ZYW2E+nzEVM1pZFI9f8=AAAAAAAAAAAAAAAAAAAAAAAAAAAAAAAAAAAAAAAAAAA=RxxxiuW8pXct7v8AAAAAAAAAAAAAAAAAAAAAAAAAAAA=cDP5g15z+03OVs9PjxwYmOfxxRNfuY+oP42fCHiRyZ4=XnvXHXB+Y1tT2EVzz3+mKacjnvWilpqKxICQSD3qZMA=PP1oY0zRtFxivp/9jSLzPitfP18rRXOfq6D+tZ/aQ10=fme0/teH/ilfDKHodWyfwQ18twAAAAAAAAAAAAAAAAA=fSv7LRH9seJRn/l3h/ma+mK3w/wEz3Cvnn4zJ/p1yP8=AAAAAAAAAAAAAAAAAAAAAAAAAAAAAAAAAAAAAAAAAAA=xx071nvkd/rWsReZXPI5zUMfCHPY1onYQw/OcjO3tTk=cYI79DVXE2MOeByaX0wOfWhgmAAAAAAAAAAAAAAAAAA=A7t3xxmnBcgEA9OmaS0H0HDvmkYZQgdaYMkiO5Rzg+s=UyMOM/Tipe4yQvt6cnrip4QQQz8nPp0qQL0R449avwM=kEevFZvcb2Ni0k+6a6Kwm6HNSwZ1ml3PI55r0bw/fsg=VKNhhgqc9D2NZVBo+svCusLr3h+wvwcvJGBJzyHHDfo=jP41sfWu6lLnppmL0Z8Ua9pj+GPFOsaNIGAsrthHu6s=RMdyN+INdT4M8RNoOr2OoKTthlAlCnG6M8MK4JPlZtI=Vz6tVldQyEMrDIIOQRS16cXzJMwCop13oRjqKzrx5qY=0Nbnlvi+xKs5AAAAAAAAAAAAAAAAAAAAAAAAAAAAAAA=vkCAnsK6o6oykc1dxNcscZCVny2wQYA/GrEUZUO48e0=9apSJkkDjuKd0BWcYz7+1V3XPAPFXFisQMM8+9RsMgg=p3BEbJn8O3rUXWqQJoaw9xiowAAAAAAAAAAAAAAAAAA=hAZSMdvSh3ApqTDLgngnnNWxg80OzFsBx2pv41KsO58=/9H4/m3YyelRYOPeslaxUt7EDhghBIxmowKasPQswJg=xk4GOPavrv8AAAAAAAAAAAAAAAAAAAAAAAAAAAAAAAA=8dsbUm0rXKTtdo5v4s6q3iL43+P72UANDqv2EbeAVt0=REPxwtLo9q0zwQxj5pJVXj61ySkpaocFbQ/Rbwzp66U=eHdLs0XaIbZFK+hxz+ua+ff2oLwG6s4FPMdtlh+Jx/M=rSskqcP66EXvJs+HtfbM0hHU9q5OblmPqaunaw2upCU=c9cfSkOcA9O4xVSa7AkSLwAAAAAAAAAAAAAAAAAAAAA=+qf2Kk3fE3X2IHyaCAPYmZKxek0XHZ/M9X/a+fHh/wA=CinvqTn8oz/jXzDB98VE/wAAAAAAAAAAAAAAAAAAAAA=fMbWM/rX07XRh/ha8yJ7hXz/AAAAAAAAAAAAAAAAAAA=6nyn4kwHf+leeX4yx7c9amNimYM65Jz1qm/Ix/Kt0hM=d9CswyDmqoGWbPTrVpK4D+w245pM8duvWjkTF0GnPp4=3SgcYyv0o5Y7XDWw3PPYUDtmnypbAh7fh+NKMnjijlQ=kFtdR46duaUfTrRZXuAkPdeMrUhYnjHNGg9iaJNvJ6k=qzGfXB4rNpAyzGevb3q9DnOetRJDuadu23HpjnFb9jI=jgVDDodPp8+0jHeu20W827eRUPYZ7t8JvFa6dqqWFy4=Ra6kQi88LN/D+fT64r3iurDP3LGU9z5x/aJ8Kmw1rT8=xVbL+4vgtjeAD7sigmNz9VBX22j1rzHTLnDAOeD1Fck=OPvNM2WyaPp/4SeI/wAAAAAAAAAAAAAAAAAAAAAAAAA=P+A13td1F3powluwpG6VcleLQjifF1ruRmPevEvENqM=c/FeLHRs61rFHmGtBULcc+lcbdWjysXlBA9K6otWIaM=Ku4do4HHpWHdQ4yD0q4smxmTxkZ45rPlQ4IHrVLUOpU=nXAwuAaqupHeqja4WIGXkn9KiYU9LgRkd/SoW5J6fhU=atci2owrx/jTCCcYo93YbRGwzyMH6Um0A46H3p+7tcI=1iC5jyhYDkGmW8mRtPXsfWj3baBYmx0FHt2pKwj/0vg=+kHzeg69aiz71kkW0QMccj1yRQPvAt3qmkwLcKfOoA4=lffH/BP7SBpvgLxn4kuMR22oamqeY5/ht0OSfQAAAAA=KSvF/wAAAAAAAAAAAAAAAAAAAAAAAAAAAAAAAAAAAAA=rHwy0g6x4x0CzxgSXSsfwrhUVGCS7Fx+JH6AnrXyN+0=NXgfxHOin7kSAnP+zyPzroxGijExjufG+tyb5W471zc=LkkdjnmrgtCmRNx1GT6mmLwfU1aS2Fq1cehLY4/XrVk=jJ56D1NDXcNDRs/vV9V/sUjHxK8Scf8AAAAAAAAAAAA=e8jToen/AAAAAAAAAAAAAAAAAAAAAAAAAAAAAAAAAAA=hEdj6R/ZaYHxD4iHcWcfP/Aq+n66MP8AAAAAAAAAAAA=/Gsbbub1IH8qxxavKI6btc+TPEuN75Arz2/yGb9aUbU=hswpxy3UVSfC5J6VskBVc5PHAqDGJGHY1QmhSOcYFNw=ZbnAqkgGnjoc560g7fqadrh10HA49KPmalZ3uxAPoM0=KMgdBxTaBDsnHQY9KcOxpIZGGJf5R164qwoAAAAAAAA=gJ1bOB61KnHWoewyyh/XtVuFiMfSpktAuaFvIcg/hW0=Wc3T3PFQ1oUzpLGb5hg811uk3OGXJ6VFk4i6nf6ZcNI=25ETESL80ZU4IYcgg9uRX1xoGo/2voenX5ILXNskj4E=j5iBuH55q8NfnaJmiHxT4ft/FXh3UtGvMCO9gaMOV3c=lt/C4HqrYb8K+Khb3Glahd2F6ALqwuHtpwpyN6HacHs=jiniI2ldLccH7tj1H4U+JhoviyzNxIEs79fs0xPQE/c=D7fNgZ9K+m6eFb96JM1rcKD0rrZBzniSAAAAAAAAAAA=NIyW4LN34rxbcs2vM6Yv3Uec3+k4JeYZf3rlb+2wTwI=t4sRzV5AeeKwruLkjFWtHoIyJ42zjjms2ZM46e4rQRU=HTn69MCqsinPbHrQkDKzjOexqu3SritREbE4wB1/SoQ=r+dUkgGnJFNxxnvTsHUacjjApjAYwB070ct3cnqMbng=wPrVGRTC24AAAAAAAAAAAAAAAAAAAAAAAAAAAAAAAAA=+PnGTzjFREcdOg5rKxp1IJB82cfrQAcqCMAn0przGyw=oeTkfdBJwa/Qr4Jm38E/sO3mrSsyNfaTqN03AyJJWkg=k/8AAAAAAAAAAAAAAAAAAAAAAAAAAAAAAAAAAAAAAAA=6YL34gWLtjFtE0n4gGuWVjSKPs3vXw5+0Rqaz+LNVjQ=bOyVhuHp6VpiXacfmZwPlnVWDSse+etYcowQBnANaQc=oindEDDkHBPtScntz3NU0k9CVsPUYAzwKsx8cD0psdk=WNG06g49K+q/2KBj4keJP+wGp/8AAAAAAAAAAAAAAAA=tiuRbeB1HU3lz/6AlfNMDEPx61nU/isUdj6O/ZYb/io=jxCueDYRn8nr6lroofCxT3A9DXgnxw5u5QAAAAAAAAA=xe8R0+p8meJcl3GenevPr4AsxzUxRRi3BwMms1xk9OM=sK2SsIhdTjke9V2BDqRxnrV2Ad1GfWmYyBkU2r6CfkI=bcY6DNNKkHgHFSlo0PzFOQ2eMGgcduAc0ct9RBjBGe8=T1JOOBg+9Pe9w0Dnjp6803JfgHjFO4A67ApA781YUHA=M4osrD6ksfOOD9amXkdKiVgJoyABnvVuNsYAAAAAAAA=knqMVq2sm0D1FLSweR0NhLjb6jvXUaZOQQMcDrUPqI4=80C7wV3dMivqP4RamL7wmtszAvYzNFjvtPzKf1P5UUc=+Kgnsd7Xy/8AAAAAAAAAAAAAAAAAAAAAAAAAAAAAAAA=nnqc+9b4n4E/Mmna5wFpMWjKA/Nj5T6Hsfzr64+HviQ=Hirwnp98xY3KIILrccnzUAAAAAAAAAAAAAAAAAAAAAA=u4zMXW7Wa9i8qHhe5rzjW9AS1V8Llu5NeJUf7xs6ads=lPMdb08gudvSuC1SzILcd62g+oNHJ31v1rn7uDGfzrQ=eyJZiXcO0ZzzjmsuaIg9OavroFtCg685I61TdD0pisU=eRSMZH0NV2B56n0FWu4PcgYc1C49O3vVxFbUZ7+9MIw=VXUBCPpntTCCeOetS1rdAtRu09zx3qvLH5i+9N73EQU=u21tpHBqySTjjJpNX1FY/9T4+cclTTGHSsUaabFcgMw=SDkdqAcKTz700nsJ22CVmjsLqVfvGMgfU8V+j/xkit8=wR+x7onh6GAxtqFpp2nhc/dkcpLIT9Sj/nUtpp+g5P0=2y7nzBpkYBQDoMCvqj9l/T1fXNTunHzRWwAAAAAAAAA=rXkvU0Wz9D6fZgis7dFBJr87Pi3eibV9Qk675W5/Grw=RrURnA8G1A4cjPQ1jyN8/r9K1gimyJstxg800MMdye8=VNXuiNCRecZ6+tTIP5UWsrDRp2ZIZTxivqv9iYD/AAA=j+J+SSNDQf8AAAAAAAAAAAAAAAAAAAAAAAAAAAAAAAA=+a4X+cexrOp/EYR2Por9ldz/AAAAAAAAAAAAAAAAAAA=X1bW9D4WKe6A9DXgHxwb/TZcDHA/kKxxfxRHT6nyd4k=P9ZJk4+lef3x5JY8d6UNB+ZiTgseRwOlU3HTHANaITs=FeQ81Vk+8h98Vpa6C+g7jp/Kkzjtn8etMBgHIHp6Uow=7j/Op5QE4B7U3jvx7etNRaYk+4Dng5xS7gAAAAAAAAA=uwmPNb0GealAC8D0oV7D2BhlcUsTZUY7cU2m2CZMjAc=IqwhGATz+NTJAyWPk47fyqzGQOlSMuQuM4OPwrRt3HE=/nis2ncLo3bKXlfTiuisJwAAAAAAAAAAAAAAAAAAAAA=4LfW5bCR8R30OUHbenP8s1EdKibG9j3muC+Mnhs+JPA=DqCRKWutPIvrcA/xR5J475QuMepFd9RXgzJbnyZbT5A=jp0YAkelez/AnxMNO8QXej3L/uNUUPASeFlQHI/4Euc=8QK8+LtNM2kk0fRNFemYDWXiub8Qad50bMBXnYynazQ=a0ZWkeReINM2luMdulecaxZYZgRisIPQ2kjib+02luA=81zN5b8t/St47GbMK7hBPQ/WsWeLrj1q13FujNlXLdM=A/lVORQVzgZp2DYqyKB1/Gqjcdc81S2FdELLg4NRnH0=CaoRE4J64PFMK4we9UNNMafboaYeMZH1NO10LQaRlh0=gBUXyn6UraWQbsq3EYRlcVLE4dQc896LNpB1P//V+P0=8cbQPzqPG6sltqWisBnoRx608DIxng9qpjujS0jTX1c=1bR9KgAAAAAAAAAAAAAAAAAAAAAAAAAAAAAAAAAAAAA=OMfZ4iMfT97+grnqw5k2vL8xvRJ+p806SgLjuc19hfs=Mlj5em6rctnezBPbGTWS+NepX2We1+ILhbXQdTmkOFQ=tZOf+AnFfm/8Qrky3UpY5LNVVf43yREfhPIb0hmPrWU=ScMSBmtoA2RFSMHGfWkBx/D+lWl1E9SRO2alTAwB+dI=a1H0NC14PoK+p/2IZt/xN8UoOg0ND/5FX/Gp3mmD20M=tf2xtRD+IPBOnZH7qG5uCM8/NsX/AAAAAAAAAAAAAAA=zqL32Edj6I/ZUlP/AAAAAAAAAAAAAAAAAAAAAAAAAAA=1r54+N0oOoTgfSssX8UQp9T5V8Q/ebJ9zXA3q7yxpIY=Y86gZqhIO38hWsV1EV3AyN3GfSq0oOO3BrRC2QAAAAA=puOevsOOlPW4xNpzkc0m0kAsOc4o0sJ73GnAGPel4Po=E+1HW4MGwozzg9BimKu/G44BPSkFyfOB0P5Uo/Wi1ws=6C4zyelMhwrMPQ0wZYTg4NTLwP5VDB72ZKpC49+tWEM=0x0qLPcd7FqA+vUnHStCBgOD17Um0h7mvaPjkn8K37A=l5GfWolZsOh1ul3GGHNeleFdZk027tL6A/vbWVZVHrg=PQ+2M1nNWdxrVWPsK1uY721guYDmKeNZEJ7gjI/nUtc=oJ80b9zE+K/HmgHwt4z1vThEIYBdNPaxr0ELnKAewHE=WZYarcadc217YNtu7SVZ4TjPzKQRxXnNJaLodEtUfa0=oGrR69omn6nARsu7dJeOgJHI/A5H4Vo16MHeKZzhUM0=EJEII4NZ14c0GNOzueeeJ9I4cgcV5Rr2mAFiRXkwZ1s=2PPdWsipbiuRv7fAPHeuqJkznLuDrkcGsO5h5I5qle8=YRlTRbT/AAAAAAAAAAAAAAAAAAAAAAAAAAAAAAAAAAA=qBkAAAAAAAAAAAAAAAAAAAAAAAAAAAAAAAAAAAAAAAA=Q1gCByR74pmB8veqv2Bsikj3KQ3celVI28mTB6Zwfek=WA//1vj4kYHX86YwwCe1Zalsqg4AAAAAAAAAAAAAAAA=D1X9nLRpNd+P/wAAAAAAAAAAAAAAAAAAAAAAAAAAAAA=fqktz8UPCOksxMFlost4ij+FpZTGT+IiH5VjOas09xs=1sjyDRgPNXP4k19u/s5WBtvARupM+bdXByPQDoP1NZU=NXmkV9hnZfEy6Fp4H1hy20tFtX6kivzi8azmS4csc8k=NFV/vXYiJ5td53H1rLPWtobDe41hmmgg9SKcVLVEipk=7HgVKv3e/NUr21KL9uc/dBwTkkGvpP8AAAAAAAAAAAA=LVv+Ylozxr9UZX/kprK9pajj1+Z0n7XV0ZPi1pMT5Ag=NEVVGP70rkn+n4V4rathh9axTbbv3Yuh9A/srzlPiPc=yZOJNLYc+zKa+x62wz1kKfQB1r5j+MV0ZtQumz1Y/lU=ni/jiOn1PmjXVLyOccVxF6uCRg1MRsxJxycjkVQm68c=6VqugW1KrjB5BOaryj5DWqYre6IOQOPSmlQTmndiW4g=2c5BJ+lMx7GjVWYxcg4wKaXA7damSle4ug0AAAAAAAA=OAAAAAAAAAAAAAAAAAAAAAAAAAAAAAAAAAAAAAAAAAA=qwexYHI5qSPB4PWk7odmTL2/WpozgDHIz60rAWoySRw=dKvQse+c5rN7jNK3fBANb1lIQRzwe1Sw6HTadPgj0rs=XRbo8AgYbg1EldDR9W/BzXf7U8JrZynM+mv5RPqh+ZQ=/wAAAAAAAAAAAAAAAAAAAAAAAAAAAAAAAAAAAAAAAAA=GyyH8Dv59xXhNoPLkGfxrmq/Gy4rQ+lvgBrzXfh+90Y=nYmTTZg8W5v+WUmSAAAAAAAAAAAAAAAAAAAAAAAAAAA=q4jJ1exW5gYY5ryjxJpW1n+X6V49WPJUaOmm7xPLtcs=DDHIrhdRtSGYVpHYGjlb23Kk8dKwbyI46Ecdq28yLak=izxH8KzZ4uPcdaq+oWKMy4x2FU5VIH+TVITIGX5ifU8=NQFSDjvR1FsQkNzjGaa/TjselXqDVyH2JppAPJqgsM4=5HNMKjAz0FOz6CIyBnPaq1zFxvHbg4o1QPU//9f4/bM=2qCVjj/61Yo0tchBG3GOe36VLCp/M8U7iaPpH9iHRZM=Vvj5DfKuU0XSJ5m9vMAj/m1dH+0rqb6p+0J4njeQvHo=bZWdpEc5CgxCRlH/AAAAAAAAAAAAAAAAAAAAAAAAAAA=LudMkGvvv4PWAsPh5pCjrKplP4n/AAAAAAAAAAAAAAA=eb9bLwHIpPzyzqFHrjOa/PXxXM0ly/1pSX72RMdjhLo=+98prNYEFvQGt4DZEV78k570ipjHpVX6CaJBk9KkHoQ=/WjYa2NG2UfKAAAAAAAAAAAAAAAAAAAAAAAAAAAAAAA=I8f+PE/hWbV2kxrr8zuf2xtPx4+8KX2D+90qWEn/AAA=Td/7Ma+f7cEOPWokrTaQo/Ce6fsxS7fitGucb9OlAAA=9/6V9r1eHesvkKfQjmlEMTyN0RSa+XPiRC8088kgIyQ=4FYYp/vUiqfws+fdfjw7+9cFfjLngg04gzDnzjkYFZ8=KD+IrWL0AqsDyOvfNQMMg1ogIozlBS4AAAAAAAAAAAA=RTQOuCKOZ9haXGFsdOvpSBcHJOTRzXQ7D+3pj8aVcn4=npScrLUBR1UAAAAAAAAAAAAAAAAAAAAAAAAAAAAAAAA=0+gE68gVKgGRg80mGtiVT+AHapYzg9BUMEi0hx61biY=IxUvuM0rd+gFbNlJ056cVEh2OispcEGus0i4II6/Sp0=0CPc/gx4lGk+JorWWULb6oogdSeDIPuEe/UfjX0pW+E=fha8yJ7mP4r0GPxR4a1XR5dg+22zxozjIR8fI34Ng/g=V8RW6SxfJdKy3ERMcynqGU4P61NdJTT7lQbtY9F+GHg=h/4R7xdp11JJttrhvstxk4G1+hP0OD+FfWFVhno0TPc=Ciukga6hlrjPEumAq5A6815mNjaSkbUXrY8f8Qacw3c=y/pXnOq2Zy3FZwehozjtQgwTgVzV5D161t2IZh3EPJM=3rInjPOPwqtw6FCVPmOR+NVHQ4GaYio6/h9ahZfUcGo=+lwZXP0qIg4AAAAAAAAAAAAAAAAAAAAAAAAAAAAAAAA=2nPXPtTu77EvYTBA5wMfrURXPB5z2xSemg0f/9D46kk=FQogOXZsAVcngDFYuS2O1ZWNG9SvJpl0trJcqjNBGBs=3C8LngZNQxjaAAAAAAAAAAAAAAAAAAAAAAAAAAAAAAA=0s8+7s7/AAAAAAAAAAAAAAAAAAAAAAAAAAAAAAAAAAA=9q/oKwqTWkO9/wAAAAAAAAAAAAAAAAAAAAAAAAAAAAA=PsXhLR4B/DbKfz5/rU0U3VuVP4PmeQftO6oItJ0uxU4=GYtK306D+VfDXiBiZWJPJpc15truRHY4254bGPx9azQ=nIrohsD3I2xuGevY0gJLEHtTaYO3UevUYzU6LkEcfiI=gFY0rRMsM96+s/2I7Yf8Jx4unK4ZdLhQH2L5/pUJ+8g=JWtodf8AAAAAAAAAAAAAAAAAAAAAAAAAAAAAAAAAAAA=LY9b/Z9nFt8VNJcsVDROuR3GORX3JI8odfKRXQ9TuwQ=cj8+M1nTlKM3YdT4URiNpbqXzTmBQFCHoT1zXg/xWsA=w3E+Vxknis60bTUn1uKlezTPmXxJEQ7jvzXnepJhjg8=etYoowLgcnPcd6zZiQOD9a0irgVXyQPaoWHXd274rS4=SivHwCMjr0p2SBgevFVuNDOhx2+lRM56Dqe+KQbO4Bc=aM9z3NOzzjjNHK3cVwJI4/PpSjsAAAAAAAAAAAAAAAA=elICcnOAapJtCViTOTxggUjgshz1x6UWdxjoWygz6VM=KT0HX6UmmCa6ki9+e+alVjx1pNAtCzGTnPTFWY2wQc8=J5xUMehfhc5HP6Vr20vPooqWuwG/Yy4K810VneCEjnI=ewFZgztvD00pmt7kuyyW8iyxbTghlORX2zomqRa3o9g=6jbkFLqFZOOxI5H4HI/CtcPdSaImi/Xyd8ZfD40D4gU=+8CBLbU0F7GFyfmY4kz7lwT+NXiFomOm90clZMWUqpw=HsfQ9q+vvA2uf8JF4T0u/diZnhCTZbJ3r8rE/UjP41g=0JWqW7hNM6Ciu4zCqGo2onhZSM1y4uHNTuVB2kmeU+I=bS9rSYFeU63Y4LdzXBBnVJHC6nb7RXKX0GCfSuiOqMk=mBdwYz61j3MWCe4HtT8gWplzoc47HmqUq5z2IqraiKo=6ke2faqrD35q0tAuQSDIzUDe54+lPfQSGvzwfzqBhgk=rRaCu9hD1pmPU5poT0RGcjgnjtTGI2/MeBRYptH/0fg=ysz9p1CMso+U559PatuVhDDLLtxIYyFNY9Sn3OltJII=LwXq9g0YZ7iJCpP8O2uEt1PloGC52jvnNKPUZ9j/AAA=Jq9z4Z+H3xt1+1iBlsbZLuJm5UvDBOwB9ecV4N4dQLo=dbN3lHnMfdjuz+tczac3Ht+v/DGlrO39bHp3giHztTs=dMZy4r9HNITy9J09P7ttGP8AAAAAAAAAAAAAAAAAAAA=rqLXPiEwB90VvCEAAAAAAAAAAAAAAAAAAAAAAAAAAAA=ssxrOPTp1NdURN9CM5AIAAAAAAAAAAAAAAAAAAAAAAA=B9c80nsO2hqWYwymvrz9idNvinxgef8AAAAAAAAAAAA=76G/hZ1P7ZK8+AmwOLi7GT7pHXzIqjzOKip8bFHY9E8=hFcpY+PtIuHO1RuGfwr7u0qWWbT4JZlCF0BVfRccZqY=n/FVhy+FF6vJ/i5Ykx+aMfOtVjFZRYqe58meKoNssnE=3rzPVE+bjHtWaexRzNyDuPA/Gs6YdfU1tF2DoVCOMmo=uw459avqSrXK44dhjr7etOzxVWSC1yBmZsBRQFxwB1o=HbYFsL3woH4ikHQmhP3QF6Y4BpVB9M4odm9QHZOcY4o=VeScYwOtF2txpC/QD3xSjnAxTuDGw5BZSKsDGAe9J6A=lqSKcjOOalU88D2qWhk65O3H41ajYgLge1T0DQuwOcg=xWlbtlge1Rsxo1re7IYJEMt7dq6PS1wwZ+XPr2qdGGw=d5odxsZe3SvqP4I6z9r0C60uRsvYzbogW/5ZvyAPoc8=50U3aomxT+E9Qryn49+H21Pwrb6rArNNpE/mNg/8snE=tfj/AAAAAAAAAAAAAAAAAAAAAAAAAAAAAAAAAAAAAAA=aVyEuF+0QKem9cB8e5GD/wAAAAAAAAAAAAAAAAAAAAA=NZcipnHmi0Bx/ifTQyMyjk81474h08qXyK8ZaOx1p3g=3POdXsz8/FcXfQYz610QZm0c7dRdsViXURGeBWitewE=kzx4qhIuc4Ap+oFKUYBOOveqrrydo4HaqQrFZ+BkAcU=QuOTnuarqJJEZHrioX+bp3qkK+pH7kU1jxx+VU0BBLI=he3NVwJJjhxwaG7bhbQ//9L5HurFLKR7yEM0bL8ox3M=2rcv7Qx6JbSXVsqq65znJ5Nczlt3Li9C9qto1n4Rkv8=AAAAAAAAAAAAAAAAAAAAAAAAAAAAAAAAAAAAAAAAAAA=Ig8I/sM+JNUuCBLrul6pdyELggyB4Ixnv91T/wAAAAA=tDtzDYWceCdsCDn/AAAAAAAAAAAAAAAAAAAAAAAAAAA=WbTAyd4GPav0PsABY2oXGBCuMfQVvR+N+hNTZHyF8eQ=H+3r8v8AAAAAAAAAAAAAAAAAAAAAAAAAAAAAAAAAAAA=yJI269ASe9IowcnOaLLRIW5MmDjnip4R6Doab2Ksa9g=4LL+lfXv7FGB4k8YDHJsrc/+PNWa+NCd+U6r9sYZj8A=uOP9KuhnH+wlfMar83as6q99hHY774VRK/xB8Oo4yHk=yMH6V9+qNqqPQAU6C/e/Ic/hQtcJ8T7bztHjbGcEg1c=i17iJp/EfIXjCDbNICO5ryjVo8M2BzXPB6GjVzlboc8=ArLmwM8cVsldiKbY6dahIAPzAYPtVi2K+P3mMdRUZbc=NgH5e59aqTvpYQoQL1FJxnGPf3FO17MEICMk45NNx68=FHLq2wTHAZ6cmgcdfy9al76oGKBk84wOKXaB05xVRus=oA5e+Kd2poCP7succGrOM9MUncaHKckdAR7VMOMYPNQ=tdg20JlIIGeo6VYjJHA7ml5WAuRuFHPQcmrMczTELGM=C9ziocQ2N2wVYhgcepNdNZSYIwfoai2o2dfpE+GXB4o=9v8AAAAAAAAAAAAAAAAAAAAAAAAAAAAAAAAAAAAAAAA=VqvqFjDqlhd2N2Cbe6heGUA4JVgQf0Nei1dGJ8WXemw=ujX11pt1/wAAAAAAAAAAAAAAAAAAAAAAAAAAAAAAAAA=M4yh4YflmvLe2p0Pex9ZwzJcQxzQsGikUOjDuCMg0+s=1E7q5zhRTAz9TthPA49q8m8SadhnGOa8etHlqs6aTvE=PLNbs8bjXC6lbDkY96uOoNHKXsOCcA5rDuIcg5Fa9bk=BjXMWM5GKy5kGOfWn0DrcpOMfw5qnIgwc4zirsLqVmE=kc1WYcHgYHpVWSAjI71G3yg4AAAAAAAAAAAAAAAAAAA=1TfQNtRiw55bipAoBxxg9KOVPRiP/9P5L0/UoR8rcDE=8yt0NdNq2orqWmWaW67zEQNqjtmueUfeQ46I6W60htU=vA13oEUSm+i2Xi7zgouev415NrVnLpaXkMoIlijyeOA=56VNKWrNHa5+jfxKsIPCH7E0Gl2rCNpNEsIo1PBaSWQ=idwP++nP4V8l2MO0IOwUCpq6W9EU3ecmtrnqvwytzJ4=ILJFBLNIAoHUnP8AAAAAAAAAAAAAAAAAAAAAAAAAAAA=Z/Cj5A+P7BvEmoY/hdgR+Oa+WNcOZWIx61hS1ihtanI=F19PxqgW2qMiuxbCstiPHILdT+FLt5z0PSqWm5JKvX0=asRgd/X0pN3Wg7aaGtaHcw45NfXf7E//AAAAAAAAAAA=/wAAAAAAAAAAAAAAAAAAAAAAAAAAAAAAAAAAAAAAAAA=R2myY7HonwiAHxK8JjsbzB/EV97nrTofxH6BPZCVzPg=6h83QnJ/hatMV/CZMPiPj3xtD+/k4ryLWEzuOK5YPRE=rLc4+8GCeKyZlzkdvpW0X1EU2XBqvIMZ3ED0ya0iyXs=lST53UdvWnnA6DFW0+g7ojbnn1pOV6AY/nTTQtxOgGQ=UUNtIOodOg70YB60lrqgewoJAAAAAAAAAAAAAAAAAAA=OGMlSOPanCnYatYZKMYPcVMOQKGHUkQ8EetSKCMZ5qU=7gSqCfr9anEgRfmH4DrSvcHYliVpceYPlHata2Pl7QM=6VDH0Ne1kJbHauhsXwFrOVgOq0qXlfSvRvD9wwK+W2E=wQVPoR0qJjR9d+H9UXWtFsb9DkzRAvxj5hw36g1pV3U=N3gmZNWZ84/HjQG0/wAAAAAAAAAAAAAAAAAAAAAAAAA=ea87sHw20nqMGuGppJo2WqPpr4U61/avhWK3kbM+nt8=Z2yeSvVT+XH4V3FdlGV6abMXuFFaiGSKGUg1w/iXTgU=XYDpXm4xKM1I2o9UeQ+ILHbv+npXnWqWvUY/SsoM0aM=jr2A5OK566h25rfdGbMW6iyTWNPHgHrxTiBRkHBPGao=UgxkgcdKoSKrocnFV3XgirvYGiBxUDvtBz1Iql2FuVE=2eY4XpSrHtHv3NWmLQd0qMjeeMcVSBn/1PiRZGJwMj0=xWnZanNaSL9lkaNlPBHFZWvoTdo9d8A/Em1i1SZvEcQ=nn3VuLf7WegAAAAAAAAAAAAAAAAAAAAAAAAAAAAAAAA=gCuiqSRxk5bj2Nc8lybm8fetY+zf2zFh034Q+HdKtCE=IpNftLeNM8+Wkcp/IbR+lfJdgmW5FKo25tdgj8J75+w=+6Mb/wAAAAAAAAAAAAAAAAAAAAAAAAAAAAAAAAAAAAA=6sAeBMelfMGtsPMc+p6Vy0vhRTZyd03DHPT9Kzy2SM8=4cV3RXYgaQWP16U5Dgev0oTTdgdySM8AAAAAAAAAAAA=J6bDvoatljcue1fXX7FBA8VeL1H/AAAAAAAAAAAAAAA=y/bDA+y+CCe15cDH/AFr5iX7/TIrOpbnYR2PQfhSxT4=JHhEjr/aca4+tfe561eHXvsdTZBWP4oiE2iXQPYAAAA=lekyIfEj4/8AAAAAAAAAAAAAAAAAAAAAAAAAAAAAAAA=1kyA4IOa1FYozMOc1TfLjJ4HatY7EkEg2lSQOuKd94A=PPNXoDEz2PemZBPOQAKlJhcb2B96TOKveNxIXORkmjE=n65xUxulYd+4oY7evFKOF68ZFCdxMUdj3xzTgTgZoWk=oGwSDKe/tSwklMtRuhq5Kp6etSqT+vNJgOM+04Tlv5U=TRJk7pCSevIqGg1uXomAxnt0q/C3OffqKUtGPXqats8=tPPrW9Yv03Vm9gOo0yQAAAAAAAAAAAAAAAAAAAAAAAA=P0+8052y0T+fGP8AAAAAAAAAAAAAAAAAAAAAAAAAAAA=X/AeoiEZubDF7B82AAAAAAAAAAAAAAAAAAAAAAAAAAA=jXXv7FQ2PW/hFrv9neIFtXci31BfKZT03gZU/XqPxr0=+rTCv3WhTWoUV0kBWTrFsJoDkdK48bG8Ll03aSPI/Es=pxUupFeX6xZEMT+dcUGdEkcPqFuVbBFczfRZJNdCe5k=swLqMDgjisW6Q5PBzmqi0LoZsyEn9DVGRQ3I61WtgRU=HHfp/Sqrj8qoRTmlVCQOT2qv5bSNls81qtBDymwYA6g=60wjGMGhagRnJpuenrVbCP/V+HYskjuSfzqxErjBz90=PWpk0iGjTt5OhOD6g45/zivoP4B/GjT/AAAAAAAAAAA=dvqvgOecfZ3uEDPpszMCHDdQmR2IIyfWs5q60Vy4Sac=ufQn7cN3vuPhxYo+Q9zeXDqORhUjAAAAAAAAAAAAAAA=pnrWNXSbuaw2Pq39mbSjHq+o3E8TI0dqNhZcZBI5/nU=9LjrV4e3I2gq7o+GvjVdefr1+WOQZG/nXzhrT/vXHvU=zUvhGcrdZOSCAAAAAAAAAAAAAAAAAAAAAAAAAAAAAAA=25qwmRg9qT2KVjWsuv619a/sTsT4y8YAAAAAAAAAAAA=x+JClsd5+2Cv/Eu8GNxgX04OfdBXy+mRJ7elZVH78hw=djvPhowj+IPg9/8AAAAAAAAAAAAAAAAAAAAAAAAAAAA=q7XGcp0/Gtq6vSkZx3R8j+P4cXM3Hc14lrifM3fvXDA=fumzVjiL9Mlqw7pioJPbpXRHUm9jNZS7bmqJx6fpWiY=tg6FabJXPoc0ZOB3pvTUS3EPXAxk9KYc47HPNUtAY0c=Axz9aTDelSndWDYAAAAAAAAAAAAAAAAAAAAAAAAAAAA=2rAeoPY8ULz1z75pabiH+wNMh+UsnpSug2ZN7mguWOE=B+NBWxPEgTB6n1qzET6cZqW1uK5ajPTpjPersHGOuBg=FRcpmlAxFbdm+NuT1qHsHU6fTpMECu10abBX0qHsCPY=n4Z6z/Z2u2MjNiORvIlycDDcZP0ODX0VW2Gbs0RNaiM=IsiskihkYYZSMgj0NfHXiXQ38MeI9S0eTdi1nPlEkHM=E3zIePVSKeIWzHT6k+k30tnNFcW7lZoJFkQqeQQc19Y=OjanFrOlWeoQEFLmIPx2Pcfgcj8KjDu0n5hUexeorsM=MKimTepHrWVePNTaGtGcB4o075iSo6V5Frtnjfxg15M=T03Ot6nnuqW+Scj2rkr+HGeB7V0R0Znuc7eRHnNYl1E=YyT26e1WtCTHmjIJqjInBz06Yqk0wehRlAU9sY71mzQ=jP8AAAAAAAAAAAAAAAAAAAAAAAAAAAAAAAAAAAAAAAA=U0xaEZHoKb09qaEz/9b4cVsAAAAAAAAAAAAAAAAAAAA=v277uCQMcCtIRJKrRuFZWGGUjrUN9RNWPQ/D3jm6uLU=stB8TXU9zp9pH5OmSzSFzZLxiNc9I+Bx2rs4LVyohx8=MXUH6bhn9K56jbd2a0rJcqWh+lXhvUdJ1bSLW58PSxQ=1kkYhjaPnaFA+U+mOOK1h1rpi17O6E731PgT4sXO/VY=8IOQZG/Dk18/6s4Z35FcVJWijR6nN3B+UjHPbiqjjjo=V1KxL0GfwY4pVI4wMnFU7XFYmQccdKnjGR/wIUh9DUs=M72AUYXvX1t+xSwHjbxYoAwdLhI/B8f1qIr3lcb+E9A=v2wFzo3hA56ajIP/AAAAAAAAAAAAAAAAAAAAAAAAAAA=hmXp5eqQN/49X6DnrWlD436DnshKhu132s6+sZA/Kto=t/Cl6Ga3PlL4iwbbifgdTXg2uxks3pXBS+E3lucHqJA=pOOvpXPzLyCxye1dMSGilJywxioJRlW469xT2QFaUZQ=OBximLgxjp+NadBXQhUE80gHTPPtTfYQznHPejOcZGI=iy2GGeM8Y9KQelQoq9wFA+nqKBnJAAAAAAAAAAAAAAA=6U5TkdKXUkcMA8AVEx8uTOOCKNBjwDIPm4X0qygCjpQ=mPVk6nByRkVNGMjjrUOwWLCcY+U4q5CR0xxUNOwzRtw=4xxWzaOOORStdB1OhsXIK5xXYaVMMqamS0Gj0rw7c/c=cNjOMHNfU3hzU/7X0OxvCfnkiHmc/wAAAAAAAAAAAAA=maleCfH7QRb6npeuwqQLpDaTkJwGXlCT6kEj6LW9dXg=Cpu0jyu0l2SfjzX0F8GdbFzo9zpMrEyWchkh5z+7bsM=6Nn865KOlRFT2PTaK9EyCkIyKTV0Bha/aiW3Ykc4rx8=8Q2PzSYzmvGkuWbR1Q1gjzPV7XDHjrXF38GC2RW0WSw=5i8hOTWFdRjJ9q1J6mNPH1GOprIu3WMknk9gKaAypFk=Lg5IwDSeQqdBV3FbUhYDHNQlCD0607aaC2IiMjnqaic=XPTH1q0xbO5FjjimkZBzj8KpBY//1/hoLjvyaeASoUc=P40rkpW0LsIdFUncARjp3q/BcGMjgjocVD1HsbNreJI=BRKoA9fSvV/h/q7Xgi067YPcRnMMuf8AAAAAAAAAAAA=LlQep9zfs3aY0Hh/U759wE84RRn5flzk49eRzXst9J4=TY3Un9yFm/IGlG6w8n6lz+M/Pj4lTiS/uiv3d7Yrw7U=ZwGOPrUUlorjOcuGyOeuOxqu5IxiulEsZxxkZp4J9OM=0qmhWJBz05qZCW47ZGanzKNWz4Ze1fV/7FcmfiF4pTM=/wAAAAAAAAAAAAAAAAAAAAAAAAAAAAAAAAAAAAAAAAA=4esZ6VGEdjpfDr+VrWjSdk1CEn2+cV+iZ61dD+I/QJ4=yEprjKkeoNdFRXgyFufMfxMt9t1Nkdya+efEWFLgda8=OpbG8jz2/j+Ys3Of0rDm+nX0roTJM2Xgg4+tV3OB9a0=ULUgcZzzz7VFCdy5I5qugrA2QKaCcnB49qoNhh68UpY=x6n1pX12DoJ1wBSdRwOO9DfQAAAAAAAAAAAAAAAAAAA=gdKcvPP4DNAWEeUrwOT2GKaQwIZ+e2KLCZZX7tPU5yA=4GaTGTg55qRO1TsFy0hORx+FW48YXaeKl7jL1s+SDWs=WjdCDUuwHRWL4AzxXVabLtK+gqH2A77QbnayjtxX0b8=CfVBLZXensRlCJo/904B/XH51NOVqqCSuj0auT+JWgg=8ReC9TtlUG4hjNxATnh0GeMdyMj8a7px5otERdmmfKk=C2drkYLcmvQfh1rn9h+JLCd2xDK32ebJ4Ctxk/Q4NeY=qTTTNZLRn0tRXqGAUUAV7qETRMp715f4msMO+0eteVg=mKVVm9J6Hlmt2nLYH6VwOp22CcjpRHYbWpyd/ARk4rk=68hxmtuhPU5q+ly22JdxPXiso2ZyXl59q0WnQWpC6YE=hQOPfrVRkwMGiw9WV5ME5Aqu69cH9atCZCwz0qI5ycg=yDTTuBE2ByBke9Rt0wapAf/Q+F0lXPP/AAAAAAAAAAA=MCpbEWBcHvz6Vcgug3Dg4HQ0pOyElqaNtONwwSABXQY=k6hJayK9tMY5kbcjjqp9s1Etg6n6V/steO9M8ZfDpYY=0kVNWsJiuoWxOGRj0fH91scH2Newa85TRNRZev2d/wA=kah/7u/Rmsnedz89viRKi3U4XG3ccYrxDUnzI3NZUk4=xTMOcjqPWoHyeBz710a2JvqM5HP5U4ntggdau90h21E=4yT8vTODVlMAAAAAAAAAAAAAAAAAAAAAAAAAAAAAAAA=MH5tCU/lMtR9tBLY9e/a9iz4J8Py/wAAAAAAAAAAAAA=yapw4z61hN/vGOOxuWL+VLaSAn5LmNv/AAAAAAAAAAA=0PjfoKeyCjuK6ZK6ZmfN/wAAAAAAAAAAAAAAAAAAAAA=5zXmUtjeR59qH3yOmK5+55P4V0K6EjOkx3JzVZ+Qc/w=qtO+or6kBJJ96roeWHbPHFaXAfnjjr24phGO+PwpNvY=QDTz0zx2NBGCO9O9rWEvMb1J657UDdngflSTdx+QuMc=86QE9BTUm9BLuLk0xnLEBeKG1e4EkcQRiccnqae3MZ4=OlF1ewaj4m+ValXjINA0SgYwalU4IOfyqG9QLKEZ+h4=atRMe3WlLUNC9BxgnvWpbP8AAAAAAAAAAAAAAAAAAAA=0xUtiO20Wchl+tez/DvWRpurWUzsBGzeVIT0Ctxz9Dg=NZNtSTRT2PoGgV6e5gfJPjrRP+Ed8Y6xYIoWETme3AA=Qojk+YAf7ucfhVPT5M8ZwT0Poex/OvLlFK6RundXZ9Q=3g3WDr3hjTb5yTK8IWXJyd6/KxP1Iz+NblehSkpQTRg=PzCitAEYZFcn4jsAAAAAAAAAAAAAAAAAAAAAAAAAAAA=XnGrW2C/HeueLNmcTqmyMHcT7CuOvRJc5CcL3ro2Rkw=zHslhB7n3rOniGeh5qubsHmZsqnnjmqEqZOR2qkxXVw=ryLweOf51WkHXjp0FUnqDICp5HU1C4wMAU47iehG2cE=B9euKiIBODWiY3tof//R+DhjBz+FKGYAAAAAAAAAAAA=UHsffvUySMuMHqeam2pKl0L1vNkhgMevFaNvcspDFic=PTmpa0KbPQ/hj8Tdc+GHie38R+FJgLhPluLeQny7uLs=xP3K9+OQcEciv0l8M/GPw/8AAAAAAAAAAAAAAAAAAAA=l4mtn7gjuvXDdGA+oGVSS9k0bx96F+q/I+KPiJcb7uY=5xz0rx6+IZsn8azpAZEvSomycHFbu1tSeog2nrSE5wA=UtdEg1JkAAAAAAAAAAAAAAAAAAAAAAAAAAAAAAAAAAA=OToI/wAAAAAAAAAAAAAAAAAAAAAAAAAAAAAAAAAAAAA=uN/vWdRe+yYvQ1Y2xATnAAAAAAAAAAAAAAAAAAAAAAA=/MA1dFe+/QJ7IsUdK6XsZnz/AAAAAAAAAAAAAAAAAAA=eGf+VeZT0RvJnnWpLgnufWuanwAAAAAAAAAAAAAAAAA=0qrJg5GatbiuQN3PrUHCyMB3rRbgL1IppYEdKaRIwtk=IP6Un86aQIB16cUg680muqGKOevHvSMVXOT9PenZC1E=hLO2c4Xr9akUBcYFKKHfUeMBhjr709SPw/nQl1FqxIA=4yPSp1PbNJjT6kinHtz0qYds0g2J0I49+tWY2ApWGi4=xPk4zWpAe3fvUPTQbNqycDbk+ldJYy4IPUGoluI6/SY=fBXGa9L8O3OSuT3/AAAAAAAAAAAAAAAAAAAAAAAAAAA=ydw4Ofyz+Nald9N3gmYtWZ4n8ftEwdH12PgAAAAAAAA=lo+PqHz9RXj1m22QZ9a4qqaqM0j8J7f8F9Yw97pLsAg=yi4hBPfgMB+h/CvXq6cO/cInuFFbkhVDUrcSwP6gVy4=LjencqDtJHlXiSwCmQ4wO5ryDxDKqMyQgM3SuGnqdMs=TU4K9015Czz/AAAAAAAAAAAAAAAAAAAAAAAAAAAAAAA=lPvflVRJMudRzjHNZ7LyeOveri+o2VHTOeKryrz/AAA=VLcRWcDPXnH51ARVoVmRuMYUZxiom4OBVID/0vg30pw=oOQR64qiSbYTtAI7EjFTIVBIHY45qHsFkWI3C4B79R4=9WoJtgGOf/1UeQzTtLjZtyMZHWu48D+LtS8G6vHq2hQ=5ilIMcycBZk/uvxyKxnG6sVGVndHceKtYi16L7faDak=Ny6A/cY9R9PSvNL1sscnvUQVi9LmXLhiPrURHPB61ro=9guA+uKUDHA+vSkm29g1JU6jI5xViMZAUHvmm2Jo0rU=P619TfsVMB8UtfycbtBwvv8AAAAAAAAAAAAAAAAAAAA=4YWLYB2a5bNj/gMlfH4++PXNRWfvmcVoaQz9jlx1C58=1Ffon4bk83w7o8n9+yhb80FXS+P5BJaGnQelbvYg8Y8=i/bjz5W9V/oK+WPEyYd/rXmQVtDd6o801RTvI965m6U=3EYxz1H5V0pk2M6VTnI69Kqtzn+tWCIWBI5x1qs3EwM=61SBhg9+opApBI7VSbEMIwemB6Uhz2ou+g+ouOnHNIA=nrn9KV2gt0GM2AQBk46UxYy2DJ26Cm3fYS0JQvHXHtQ=77pP6UN62D0F2nHPGeetP64wOn6UeYWuIG2y8fdPtVg=Wk9BokHzHPPXrUqZA5wcnvSYE6HkAAAAAAAAAAAAAAA=BGfWtO2bkZPtUPYNzZtSOnNb9i/Q9/SodxnV6ZPgj1o=9A0C5KsuT1OazmgW59D/AAAAAAAAAAAAAAAAAAAAAAA=FehV14d3pozn8Rz/AAAAAAAAAAAAAAAAAAAAAAAAAAA=zJyemSAM+hNfJULkkNjBPX2IOD+tZYhe+XD4TtPButM=aLrWn3+fkikHmY67GwG/Q19QBgwDKQVIyCOhFPDPdEw=9xaK6yAqKcqsbF+gGTWVa3s3ca3PKPE0FzqMrrCpWP0=elebapoqwBiRl+5NeVF2Op6o4jU7bBPFcfqUOCeOa6Y=O5G5zl3Ec471iXae1XazIMiePis6RD361QylKhUn9ao=rpj8KpN3DQryZwO+RULAfjVNtCS6kbLkg+lQkc8Dv0o=tbgf/9P4M9MUq5Kn86YiRScAAAAAAAAAAAAAAAAAAAA=VcdyMfWrEb4XGRk1PmF3YuRT4PJxgAVqWtyVHDAc5HM=1pSTSBM6nR9UaJGhclonGGU9vpUOpwGCQZYMrDcp9RU=iotPQuLMqTllHX1qJjnp2qrSS1ZQi44H9adz05NPX4Q=dyVeSvT86soQByQKGrLQDRtF+YYr6b/Y1k8r4tXicYk=NFcdepDof6VHVFJuz+Z9A/taJv8AAAAAAAAAAAAAAAA=Qfn5NTX+IiOxqxANbTA/88z1+lfoD8PrsX3gXw5OFZc=dp0Iw3XhAAAAAAAAAAAAAAAAAAAAAAAAAAAAAAAAAAA=vlDxQmZJOa8xfE/mbLZHl+rL8xPTmuYukwTmuiOyB34=hmygkVUkHGD34q+thEJHOR0qrKPnU+/ariEr2HZJA6c=1zTNpPXAotpoLWwmDSdecCjUBM8cVCzszER9e5pWutQ=aHpHg5Iye/FPB/vdaaTWoB3HSndOhFHUNBQ2Dnj3p6k=B789c0NMXURxjaTxtPQd6mU5oSfUESKc455zUyHIB4w=1Mrgk7ksfBGSOasqeeecUndsZaiYcEcdMVoW7f0PWoY=gNe1YgqcjNb1nJjmokM6bTpfmXJFdvo0+NvNTIFueyc=w91j7Dq9lKzfKz+U/PAVuMn6da98rbCvRoie4V8o/EQ=0H/hHfGWrWsabbeWT7VB8u0bZOSB7A5H4U8StEx0+qM=J0+TICN0Iwa+nfh/q/8AAAAAAAAAAAAAAAAAAAAAAAA=2sqDtUsOe1zp6K7jIKa6BgQelROKlGzAwNasEMJ8pAM=g9BXk3iKzwW4wa8hx5ZtHVF3hc801e1wW9O1cTqUAAA=frW8SWcvexdcYrBu04wPzrTVsgyLiMjGPu1mTJhsjFU=faKM+QfKAAAAAAAAAAAAAAAAAAAAAAAAAAAAAAAAAAA=UbrzyR3xVapiTP/U+DF7+tHQAVRKJE6csB+FKuDjI5A=c4H4UgepIis7ZYEepq1HHkY6nrSbVgLMMUipgZxmrkQ=jrgFW3EZ6dKnmXUVjRtrl0AySG78V0dpLBfW3kXL7SQ=5R/7p/wrJ36Db1ujHuopLabyZ12yjk+49fpUPTFNpvY=NE76gAAAAAAAAAAAAAAAAAAAAAAAAAAAAAAAAAAAAAA=pH9kCQL8Y4UB+9pcw+vQ1L+JFrRM+lv2qlB+EdyxOAk=f27Z/wAAAAAAAAAAAAAAAAAAAAAAAAAAAAAAAAAAAAA=Mbj4a+F3Jz/xL41/IY/pRT/iIcvhOxorrMzzX4rw5tU=HH8Sc18leKox5sgzxXmRfvy9Tf7KPL9XQA4xniuUvFE=uIPSt1sIypgNxPQiqhHNaJi13IHXr0yKrzD5ePWr6A8=UAAAAAAAAAAAAAAAAAAAAAAAAAAAAAAAAAAAAAAAAAA=aeiCNcKAAAAAAAAAAAAAAAAAAAAAAAAAAAAAAAAAAAA=gfcXrj9akVRzg076B5sGGUIFOhYlR6igRMOe1TKMLSY=VfSxIuDgVYTHB/nU9BdS1Aeme3Sr8DA9u9Q9GVbQ1LY=bnNblnJkAZ96h2EdDYyfMBnvXY6RMAUqGM9L8OXO1kw=HuMV9MaFfjU9Hs7rOWeMB8nJ3Dg1WGdptMma0TNGvG8=49aIrW2k63GgDxSG0mbnJVvmT8AQ3/fVdNde4xQ+I8U=LVtjgV7P8GdaEWpXumSEbbtBLFz/AAAAAAAAAAAAAAA=mVJXR7RRXpGQUUAVruISRMCM8V5j4lscliRxXk142qs=N6Xw2PK9btMM5I6GuD1O2wAAAAAAAAAAAAAAAAAAAAA=uouvHH8q13RJi3UZ549qyZ4gOBVLoO5myrtHy9+aqMs=ntVsRWdRkjFV3XgjAqiWyEjHeoyCCT7elUu4mf/V+C0=QO9OUgnn0pu5IqLk/McD1qwBHHnvSd9kPQl3nHygU9U=mIyP0qegPsTq754OPrVuGeRRgMcjpj0qbdhNlyKcqoE=MA3GOe9adncxs2wHYV6HtSYutjclg/tW1EZx9rhGYmA=c7x/d/wrniuCQQQR2NQjWIKBnODSihNq5SJU+U4J69o=rCnjiq8x6GjajLDPevoX9kh/L+NumDp5mn3AwO+E71E=e8kGx9V/tQweb8GdacdYZoJP/Iqj+tfEWf3gPqO3apo=z98mOxr2R3KQe47V9z/A2XzvhN4XYnOLZl/KRh/SlT8=4iHL4T0GiuwzOC+J0RfTI244DV8keLIwJZcdq8xaVJc=qb/ZR5TrK43D2rkbxdx4Bz3NbRYtDIlBYfrVRxkHPSs=VPUOhA3Trz3FQyjKn6VSBkY5Awe1BHYDmnbqTsRs6jI=F5ameXvILjnHTqKTb2AfwAAAAAAAAAAAAAAAAAAAAAA=RixijryBS5H4g0NSC6HduBmlHGdwGfQCiKaTTFuPGPU=psJPI5461YiwpwcjpUiZzkY96llInUgHkZqZCOcdKjU=vqC0LMWcjjvV2Jhnjg0nqxmlauN2eo6CtuzfBUnHocU=RJAjoLGQbh/nNdVpU2CpzUtC6HoWgXO0x89a+hvhjqU=59hcWbsCUIlT3B4P61NJpVEwl8J3lYnjDRP+Ej8L6ro=WozJcW5EYzj5x8yc/wAAAAAAAAAAAAAAAAAAAAAAAAA=HYg4NdF4f8QzaJqNrf2Y3T2zhlGfvDoyn2IzXmS1RvY=1PrCCdLqCKeE5jlQOp9iMipK9SLvFM5wopgNYZFcj4k=LHcjNjtmvOxqtJSNaPxWPIvEFmVLHHSvOtWgwzcY5rA=i9DVo42/h5bIFc1dRkZ9K3RBhXaHnI/Gse4XPUdatCM=NlXGdw5qlIOvApiKkgHPBBqCQYU5rRag1oV2AAAAAAA=DVITP//W+DAox1pwUntx0zVXEOUclmpyvyCxB9vXpSI=N2SeaGI+bg9RTllz06VLKemo4SnHIx3qZLlh9e1Fl0E=NE6XR2ncT7VahuSTkcHgGpCyNvTb6SzCmNixLbj71uY=oww6tbtfWamO4TLXEWQdw4+YVk1rzDi1sc/79fSnrjE=7076WNUSRj5u9WF7VenQOpoWvLDOa99/ZQlC/Hbw+hY=+/Z3eB/2yJrP7SK6M+wv2lAT8EPFxHVYImH4Tx18JKc=5lIHYVFX+J8hR+E2NPwSM+tfa37OlyZ/hLoyH/lhJNE=/wAAAAAAAAAAAAAAAAAAAAAAAAAAAAAAAAAAAAAAAAA=F+9kGOTmvNatVkbR+E8j1lMFuMiuNvRyfQ81pFOwXMg=l6EnP4VTYcfWtkJkDZzx0qFhnIHSrQXIoxhCe/NMclg=4XJz3xxQpXFogWPYzED5j1pSPU5+lK1mPoJjpzSYNU0=paMkcBgc0m096z5igPXpRzng8VonpqIUcrwDz7U8dBg=6mjqHQeuMU0HZL7NRYV0Tg5xUkefXOe2KllEqnnp7VY=EBBwBj8KTaQmTruA6npVqM8gDrmpfkUjTt2GQMn1rWs=R+nPGR1qGu4G/ZyDj+ldPpsv3SD0qOgjudFuNrIPSvY=n4cat9k1a1y2ElPlPk4GD/gazvytNFW0se4UV6ZgfJ0=8TNAOgeNdVtol2207fa4Pk2jEnJA9g2R+FYmmkRt83c=rzZKzaNnrqfTXww1j+1fCsETtmaxbyG9do5U/kf0rso=u6i26auZPcKK0EFZmq24lgYY5wa5MZG9O5cHaSPJvEk=ZBWfGMZrzDWrT72PWuGDN5HC6lD96uXvYyDzXQmQzn4=6jBB+lY9zHgHj8KtPURlzpx/Ws+UDHPBqkLrYpyg+5o=gcHHI/OqXQRVkGOvU9ajbkHtxVi6H//X+EAwUDAz60w=ZieuetV1JDr0ooAXB/PpTo+g/wAAAAAAAAAAAAAAAAA=HRQP0qbgiaPIwWBK9TjrVq1Us43fcUcihrRg7WNK2jI=rb4yc4AwelbNhcSWpMgzuPY8j0x9KylZ6BsWNQskeFY=+sh+7f8AAAAAAAAAAAAAAAAAAAAAAAAAAAAAAAAAAAA=au5StcuwNt2k5ye1e7fsqqV+PXhJic7re9H0/wAAAAA=tD6M+0f2jEMnwT8YqBk/ZFP5Soa+C1beEYcBlB/lUVc=+J8hR2NWwbDLivsr9mGUSfC5EH/LLUZ0/UH+tKm/fQ0=r3T2WiuwyOb8bpu0KX2NfIfjVds0mc9a8+f8aSNo/Cc=j2s4DNjPSuKvRjIBxg4rSIIyZgRnAAAAAAAAAAAAAAA=euOKikO1c1a0Wo2isoLkjtmpCmOlJRVxaDR096Djr2M=zVNILidOaTHOQKn4tw0AAAAAAAAAAAAAAAAAAAAAAAA=S9AHryeQPTpSAAAAAAAAAAAAAAAAAAAAAAAAAAAAAAA=OPWpZRMo7jPp0qRcn8KnR7ivcsx/dFWojyuP5VLQ+ho=EDZxg8Y71q2r9MdBUyWoXN20fHTtXRafKeKy1DqdlpE=P8yZr03w3feW8bBsbTkGs5rQpbn0loupRaxpVre2770=JU5PuOD+oNX69Cm7wTMXueN/HzRQ9npWsxoN8UptZm4=clW+ZfwBDf8AAAAAAAAAAAAAAAAAAAAAAAAAAAAAAAA=2LtiG/hwBngSJyP0yK93rfD25bGc9woroJCopk3KRWU=WjeDQ1ueeeJrEqXIHB5ryfXbXBY15MDqep57qltlmOI=uRv4cdK6kZs5u6TBIOax7lO3P4iq6kmTcRkE+lZsqAM=Z559q0T7C3KciYzuIz61UZQB0OaadxkEin6GoG/yatY=xKP/0PgsN60Z+uaqxGo4cDmjpSGh2AQcdcc0BscAAAA=/WgCSMnGRnOQOnFPOBxkilZXE7kynOBjirMbuOcZFJo=XUov2038IyAcA81qWdwMdznqah7E9Te0u48uUI4LQSA=KSqD1U9az9RsG028MIcPGRvicD7ynv8AAAAAAAAAAAA=bHXNTB9oA53dK0sal+0GGy2Ca9r/AAAAAAAAAAAAAAA=0k0X/fcLL/Ws3uPofdHx8i874OeMkGf+Qex49mB/pX4=fcbgxxHplBn8qiqv3vyFDY1bFslefSvsH9lW6EvgLVI=DPMWrytj03Kn+FTH40P7LPdKK7TIwvF67tDuB6EGvkE=8cjE8npmvOn/AAAAAAAAAAAAAAAAAAAAAAAAAAAAAAA=yRiqTcVotgZWkYKTt59qr+Xk7pDk+ladAvcYoIlYAcY=OppQAAAAAAAAAAAAAAAAAAAAAAAAAAAAAAAAAAAAAAA=jl0DUAScYx0oHSqirMGP+9nt9KM4x3prXcByMeBQ3KE=OOmMU13FYkjclVPFSCkUTAnOSMDpipF69elT5hctJkI=jHtViJj1/GpaDcvQNwvpWnbtnb6ZqOojctJDuA7Vv2M=JyKi2o+p01lqCW4Xc3PoK7LQri4vpFH3Ic8jsaiSGfQ=x8K5449DksEbLQPvBJ5Ib/69d3XXQd6aM5bmJ4w0Q+I=PwvqulrnzLiAiLnHzj5l5/3gK+RNrxsfMTa6naw9xwc=9axxC94qOxvaDfS6fe2t5A2JbaVZV49CDivrO2uI7u0=4biE5imQSIfUEZFPDP3nEU97ktFdZAUhGRSaurAc34g=bQSRkheo615D4htSC+BnFeNa0mjpT91HmurWxBbIHFc=F38J6Ct4knMXkXOQOKw7qM88c1o9yTHuV4yKzJo+54w=VYFKUAjOT+VU3Xqc9acQK0mRnnmoXXBPP5VonoJdz/8=0fgsDOMUdQOtUyfIXr60A5pAApy5BGMc8c0wJFKrkcE=9fQ08OFXgdTnnt0qWrh1Hq3XJzUyOD068YpboLdy7Ew=FXkcg84NXrSX5mCnkjp1qelxWZrWE+LZHGOTg49c10g=iLrOnPbMg+1QfPbEE5YnGV98/wAAAAAAAAAAAAAAAAA=UZcEH0IqWNcLn3FEbGupo27YC8fhXq/wIufJ+MfgJgM=l9UVDk+oI/rUNa3H0P0L+M1ubn4UeM41GSNJnf8AAAA=Lf0r85oJAba2xyfKXp9BUVf4j9EKGxqWTn5cV9Z/slQ=4bRvFMAzmO+jfn/aU/4VMfiXqPoz6KoruMjF8VHGh3U=7gV8geOv9fJ9a86p/GZrH4TxjWeCea428GWbGM1qg1M=GnwpPpWbKxbCxjjua1QtiEKFOcZPrTTxVDK7/wAAAAA=pR908fmafQQzgdOgoA7Ac0+mgBzjmk75zxioUhsMUcc=OMA9KbSFfUTPGBSg464oXxBrYUHHH9KUEd6cUAo/LvU=KAAAAAAAAAAAAAAAAAAAAAAAAAAAAAAAAAAAAAAAAAA=CpCxNHgfMTwO1WImzj3qb3GX4GAb+laFu4DDA471HUE=GxbTBAAAAAAAAAAAAAAAAAAAAAAAAAAAAAAAAAAAAAA=LgAAAAAAAAAAAAAAAAAAAAAAAAAAAAAAAAAAAAAAAAA=+60RPcK+ffiX4L+wazc3NpDiG4cyrtXgZ5Ix7HNGKXs=qZVLdo4ayRoJgrivpH4dXwvPC1rHv3NbZiyTzgdP0OM=8KyoN+0QT2OqorvMgooAAAAAAAAAAAAAAAAAAAAAAAA=WVqrRvT+E8q1q2AZ2I7muG1GHDEYrSI2crexDPNYF1E=gZ/nWhHUxbleGA4rKn75/E1Ss0O5nSr7dKpyjnIxzVo=1YrlZh+lV29lwaqwH//S+C8cUAke9VYQoJ5FB+lCQnc=AdKcn3gKGGwDG7jp705QAxB5HtQguTx8qM4x9aeGxjs=Co1C+hOkhCADrVmOTOMcEHqDU8uoKRrWMvygHgE5HtU=u2F60MylflYYOQec1EkndCbe5f8AAAAAAAAAAAAAAAA=HXf/AAAAAAAAAAAAAAAAAAAAAAAAAAAAAAAAAAAAAAA=+lfhF123DHPQFsf1omrI0jrKzP0u+KAz8NPGgP8AAAA=8/8AAAAAAAAAAAAAAAAAAAAAAAAAAAAAAAAAAAAAAAA=elfT/wAAAAAAAAAAAAAAAAAAAAAAAAAAAAAAAAAAAAA=Yniw40O6z6CvkTxyoM0hPXJrzqn8Zm0fgPF9ZGS2PWs=ir4hC26tFYRhzqz9eB/Oqh4GK1S7CepXbg0xs+1Wh9A=rSZ3r05PrSn1FNK+gCHpTQcipSsgA5IyBQfpzRJK+gk=O4HpmjjnND12GIOR0oznGelKyuIXuKUdeatKwC8E8Yo=kU4PU80OzVgGqMTNnvzVhaGCHgj/AAAAAAAAAAAAAAA=D63Jl+matIwHJx6VDQFqIn5eM1cW6WIYHLZ9am3QE7k=dtfMuCDIdqHnFdNpwWMDaBnjNTIEzp9Pl6V2OkTklR8=rUPbQD1PwbeMt3bMCQ6OrDB7ivpZHEiI69HUMPxq8M8=32hT2Q6sPxVpy3+lSFhlogSPx61tiI3pMVN2kj5q1eE=az1F1I716t8IdY/fTWDn5ZU3r/vDt+VcdN+9Fly2PW4=ivTMQooAAAAAAAAAAAAAAAAAAAAAAAAAAAAAAAAAAAA=891SDG4AAAAAAAAAAAAAAAAAAAAAAAAAAAAAAAAAAAA=zwc1UY9SrmbKMA4HJqiw6/StEtBFVwfT9ahc+o/IVRI=z//T+CvoaBVokKB/OkDF6UoHA96AHquRwRkdBihRgqQ=+tK4PYkVSU+6T0989KnSFznAwP50mxWZMlpMgXCnA6Y=RU6QSJyR+QpcyG30LsPmpsJ+U5ABI7cVqWcpR23Yzng=qXZ6itqdZo9xHOHtbrBgnUoxPUZ6Ee4NYN3aSWNxNaU=xgSwnaxA47YI9sVC0bKiSwk7gfWug8O6kdI8ReH75Tg=W31O3kz3++KU30No7o/Uj40XgsPhL42mJx/xJrlP++o=Mr/WvzUsm/0K2BGdsagkfSs5r9635L9Qhsa1k3zD2Nc=0h+yPchfG3iW3JH73To2A9cMP8aiWiuHU+vaK7jI5/w=ZNt0SX1P8q+SfG3MsmexNefP+LI2j8J4trbgMyryTXE=V3Fli0hyfetFYRjzYXOeeaouOee3tWobFckfwjjtUZ4=ee1XYTZXm4wx4HXNLxjjGevApWV7sV2Nwc8fypuM4o4=t0MX6Y4pPcUvzBMOtIBn8+Kdrahe6FwQc5FIMdFGPoI=p1vcW4vOB6/SnD6fpWmttRi9O/1p65Gfp6UltdCaGNw=MrfhVhegzQ3qNDxnPB4qZOM4ORSYakqEgDgdanDhAAA=AAAAAAAAAAAAAAAAAAAAAAAAAAAAAAAAAAAAAAAAAAA=v+FQ1oPodBZSdMe1dbpMxDJ/n0qHogPUPCc22eIk85E=ivqPT5BNYWrqchol/lSw7/e/IU9kWabJGsqMjjKsMEU=d00nFpma0Pm74i6Y1lqchxja2DVbwPqzabqtrMvVZBk=B6YyK8qL902ktT6ajkWWNJIzlHUMp9jTq9ZO6uYhRTA=EPIrn/EFr5sJIGSa4sZHRM0pO0jyDxHaFGfgV5pq1uU=S3FcsHoaNHE6hDya5m9jwTxXRFkswbpcEZHPvWNdR8k=x3NXC4jMmHHPJ9hVB0znAp+Yiq4PXtVeQ84PetEiT/8=1PgrGQMUYxgY5quZbIkUHvQOcUg6i8jkDr2pc9sUAAA=DkdcVOEUY3Yxnih7hYsKwGAq/wAAAAAAAAAAAAAAAAA=dJnB2gAAAAAAAAAAAAAAAAAAAAAAAAAAAAAAAAAAAAA=EaEkLtz2I71PLYbZqWm9CGXG3uc1pa9ELvTYdSQFpYg=iG5wf4T91v6flUXXMCdmYsJ24/lmrF25SyaRTgxMsg4=O6kGnPU3ifqD8WJ7jxD+zlr92gL3F34cFy2BnrGrsfw=smvzzsmBs7crnBiX+VZTs6nyX6kxNa0ONuete8fst3Y=Lb4pumQoudNdT74IxWc3ozSO9j7Zorvi7pMwOZ8cSbc=RXBwBknNfJPjRzM8mzp6mvPm/wAAAAAAAAAAAAAAAAA=1x1+uen41rFpDRhzAZ/nVB+MkCtFsJleQAE4qLr+FWg=SWhDKAU55picgbTgY4p+oegYpOD/AAAAAAAAAAAAAAA=pbsAAAAAAAAAAAAAAAAAAAAAAAAAAAAAAAAAAAAAAAA=rThnFWt7AAAAAAAAAAAAAAAAAAAAAAAAAAAAAAAAAAA=KvqMYqVWHGcZpMa1AzjpGMnp7VNHEzn96cg9sUmg0Zc=4sLgBcCr8Ddu9ZtjS0NGBsYz6Vs2snQj0qW1YfkbtlI=crj+ddVpU2NuMVMkrCR6P4cvPLdGzzxX054D1IahoUY=uctCdv4dv1zWdN2qphL4Tp6K9IyPJ/i3pPmL9pA4des=7gV4vp05guQffkV5P2mvM6OiPp3wPqg1Xw5aPu3PEvk=bZOTx0/Sujr0aLvTTMHuFFaiCqd/D5sDCufFRvTZUXY=kjyrxPaBS+RxXlWtQAEkV50DoZwmpwjceOBXJ36Yyes=XTF9DNmBdJ1xWHcJjOOmcirixGZMOpx71nSjg9yapW0=gKkgHULn15qq4+bPHP6VcX1FY//V+CxwMjrScnk9KaU=Ym4c9aB9KqwrCrx9akVGPIB/KpC/VlmOxkfHBwevFWs=7GFYea6qcA4J5pXJbuWFitkIUMD9RUiJEOBg4PFTa6E=yv1JFjQ5PB9ad5YOeBntStYm7Jo4VAAAAAAAAAAAAAA=crwB7VMl0ZS8jUs5nKDjk/wjsM10+mGOdZbSbBt7pPI=nz/DnGD+eDUSXVDT11OZEEttNJb3CgTQuUce4qe7Xfo=dMuPvAAAAAAAAAAAAAAAAAAAAAAAAAAAAAAAAAAAAAA=dTut9mP1r8ydKQrp9svO5F2MM9wcf0qasfeTXYmLNa0=Qcj9BXrfwDvTZfFPSWPAlgkT6nGaxmtDWL1PvO1lE9s=xSA53IDmpq7KTvTTMWrM5PxtZvd2BLMdiZwo/rXy540=LUq8gAwtefd+0dzVfCeN63EAAAAAAAAAAAAAAAAAAAA=cdaz5Bx74rVJ2E2VnBxux9ahOfStCU9CKRcoeOCMYqI=j5TnJb2oavYExefTik6LU8rbDqHPHHbrTSDz6U+VtDc=5CjoDik/DrRysSYYxwMmihRe43IXBAJ5oAx06mqSeok=jgrYzTlGcik4voO4pG/hT2pICcDI5zTQiYuE4J59Kas=5k2OMLmhjLkcIXnvVlMZ4zUa3DoWUJPI5q5DyQR1qJI=fQadkaFu2OefT8a1LZuV5OaTQXN2yfOPyNdNpsmNuRg=qN9BHc6NcbWFfQnwk1TM8tq7cSRjaM96xfuyT8xvU9Y=6K9QyOZ8daf9v0OTAyY/bsa+ZLyE21/JGeMNxXm1ItU=aRsvgR7J8H9Y/fS6fIf9ZHuQe6//AAAAAAAAAAAAAAA=3CiukkKZIuVrOsr02gOA8U2J+cgcV5Dr1ttL8dK8iD0=TqbujzzVYMFveuQ1CIgnArqhqZs5y6jPzVh3SbTz61Y=hGTcKQdv41myLx3/AAAAAAAAAAAAAAAAAAAAAAAAAAA=/9b4K70dqqxI4AtgAflU0Vuzc7Tj6Um7ICyloI8tKyo=j3oF3FGAsEW5s9W/wqbcwbojkubhwwJIXjIAAAAAAAA=gkgcVVlYNhwySG6HvUoZ+fTPrSSRPqSpK6jr+FTx3Tg=OP4TUtdUNlhL324ByT6ipxc427Tl8/hjj/69K1/UGrY=xqWs2XG8HbnGfyrobO42FCOvr/KocdBXs9S94jgD3Vo=ajEBsvI8SY7SIAAAAAAAAAAAAAAAAAAAAAAAAAAAAAA=QdE0wp902kWPpsFflm9kbO61G2I/1N7PHj0w54ora2Q=KO5NAAAAAAAAAAAAAAAAAAAAAAAAAAAAAAAAAAAAAAA=kvoTDB87R8uw+6PbNdCBitcK5OPkRUVpGfrVt9p0+dM=HO3Ir5e8fWOyWUYxXNWVqzLhrE8L1yEh24rg9QTDHBE=WqFa5zt0pyfT6VmypyTnrWkWJorPkk4AAAAAAAAAAAA=G98c8Cq8RI3ADGP5U7J6MQ40npik1YYnX8aTBz7d6Nk=2EwxjGKMDr+tIYHPbFJ3xmqj2AXaASQB0pw6DPTp0ps=6XEKeccc0o46UWdw0Y7cEGe3Tkc1CpbJCdDQDRYSEA4=X59c1YX+HHakNEy8r0xUwPIzUitoWI/uircRxjvipkM=TLsDDIOPrWnbtj6dKh3A27KQV0mnSY2k8+lT1Gdhpc8=hl5r1vwBrBstQtpAcbHB/wAAAAAAAAAAAAAAAAAAAAA=fQ0+vSg7wTMSC8txd2k0DDIdSK+X/HWnNZ6nIyrjJwQ=YrixMbVFLyNqesWibwHrB0vWLOfcMI4yCcZHevqBXWQ=VXQ5VhkH1FXhnq0RNC0V2EBSEZFKSugOZ8R2xeIkDtU=494htcbuOK8VK0mdK1ijzTV4fmJxzXF6gnXiuiN0Scw=XiDPQVhXaHk449K1JMi4TFZswwMVSEUphzgCqrgdRio=lcdj/9f4NETHsfyqaO2Zsbhxjmm2SxytDCepYjsKbJc=cjgKgCr7UCt3ItxOc55o2nH3Tj1xRoihUGDkipc8j5c=9KGTJXHAblBPIPOPWn4BP/1qQl2Y7vgdAAAAAAAAAAA=rXHAYHIqaFQF3c7twwMUmJmpaJvyx7YHua27aYkJk8g=HT0qJPoFkdgE+3eH76BGy9sq3SgdcD736H9KwlbdZOw=OmAcntyDWO6szWnsfr54SkEvhbQpFOQ+nwMD9Y1r83M=xrZjT/HXjGzXn7Nrt1F9cSGir8URxRjQgbvqfSus8H4=D4n0QM5QNdqhdeozWcirH6CeCrSKz0ZUt0CqXPPrxXQ=dbYb+GRP4hrqHUqehGK+dPibp4jnlwPWufEq1VMqGzM=518RQkMx6D+Veeakm1j2zTWwzmbkHOMc9uKzJu2OhrU=TQFJ+Mg96ibkc961QNEb/p3qqnE7j8RTQrIk6DpTevQ=+lFwsBHpSc9h+dZ3Qg78UH6UIaEAAAAAAAAAAAAAAAA=wDTqq9rISFyPwqNpgD8vPanF3CwqxsWJduD2pwUI42A=wDijbUGWhxjA4p4PIoY0iVDg4xmplbdxg5qGgZOjYGA=HPP0q3C2M+vWk9Ux7FyFjj37GtC3c4GcZ6HArNWA2LM=bkZrpLF8baTV2B1WnTZ2+1eg+G73y5ozn0rKQ0fU3g8=1D+0dAtZGbc6Dy2OfSt6uvDu9JGUtwrwz4sab5d9PsU=OG+cHHGD2rPFL4WXTe6PKtOnMFymTjmvqbwPqw1jw1Y=c27c8Q8pz7jp+mKig7VEkE9joqK7jMKKAAAAAAAAAAA=gryPxHa4MnGK8eppVaN4axPK9chwWOO/FcNqack4xWs=EGctephj61z12pGa1SJMe5UVlzDjJ6VSdxFKXBz/AAA=pyKAapaAf//Q+EjPtP7tQKiZ2lOWJNCVhaiAc5p6Dtg=PTOBTExcnGDz6UgBJAwT7UB1HogLEe3QmpOePXpj0qc=W5LHAAAAAAAAAAAAAAAAAAAAAAAAAAAAAAAAAAAAAAA=/u/l+VTxpkgAAAAAAAAAAAAAAAAAAAAAAAAAAAAAAAA=aTVg3O48LToNQiimz5Fx+5l9djDaf51i3Ns1hDqVo3w=zWsjQkjr8pxWD6lw3P1t+Hr+Z4B8KOf4tHtT/wAAAAA=Pv4pQGH4rePQRw2uTOOfU5p1fhiy4qzaOXjXJGea6Pw=Ot5Ot6Q4P3byPr9awb0sX1P0V8NoE0uPb90sSPyFa9c=Th/4aM5fExD0rxv4r2IE0rAcHnP4CsMWtYsqnufMHic=gw7DFeZ6vHhyT61Mdhs5O6XDZA7VkzqfQYFaq1wZUcY=M8fTioGHsetaR0FZkTkg8ce1VcHzgecEYqnsIl5Uc4o=bg5+tTypdRjWyB75FAz6fSiysP1DH0ox61Itg+o69KI=qsGooHr0phkVe+T6CmtxK43Dy4xwMc1KkaqOPzNJ2tY=uPVkijvjiklB2qQO9W1cTJkOR2p4/Ch7DRKpI6damRs=jJHPWocdQJk+YDA4HerKHBHPNTbUPQtwN3I5NX7Zycc=HvStoxmrbPgit+xkIC/Ws3o7g3odTps33R9Mmu30S5w=FMcYNRNajWx9GfCTVleOazY43qHHuf8AAAAAAAAAAAA=Zy3CuH+Jmmi70gTBclAVJ/Uf1qsUv3dx0/iPmecG3u0=lPZsV7j8FtYDfatPcjEiCWPJ6leCB+ea5oO0kxy2PX4=ivRMwooAAAAAAAAAAAAAAAAAAAAAAAAAAAAAAAAAAAA=6+hrgNWiAAAAAAAAAAAAAAAAAAAAAAAAAAAAAAAAAAA=vWTKuAeOnTiqQFKVccY5qlKuDwKqImf/0fgoDAAAAAA=ODjNWyEOBxk04PtGMVI2rhkbffNKG3HHr1I/ChCaJAE=VOepPFKDyO7e9S1cgkC46qMH0FOzgChaaFbsNygCnD4=bAP1GaZT8iQdsdcjPtUynC5bk1NtRXaLMTAMo9OBzWw=WZ2hSOc9SB0qZaAlY6jTJAkkbLj5RkY7mtXxVGn9q3o=y4/0u1jnI6ZZlG4/nXPUuaU9z9QPg7ff2j8KvBtxnOc=SLdP++UC/wAAAAAAAAAAAAAAAAAAAAAAAAAAAAAAAAA=XuRLfxs4OEHcOhxWzZv5MtvL/wAAAAAAAAAAAAAAAAA=MHRrNwAAAAAAAAAAAAAAAAAAAAAAAAAAAAAAAAAAAAA=wT9Kyxe0X5jhufKXiyHa78eteU6unLZXgVjBaFM4+8U=wOnSsecAAAAAAAAAAAAAAAAAAAAAAAAAAAAAAAAAAAA=BxmjdhZknvj8cU0+x7UOKQXEOKTA6DtSe1rCe4pOMcA=xSD35pW0AAAAAAAAAAAAAAAAAAAAAAAAAAAAAAAAAAA=T20F5Eq+hxTiR3o5dQQvQcjmhwGQ+tPpZDYsJ45HTuY=pxT8hIkUjjI5qZTjnI96lj9SUHGM1PGcEe/NTbUZajc=HQ8Gr1u+DgEj0xU2toGpqW79PatyxkAAAAAAAAAAAAA=Ga7PSLj5lAPNTK24dD2T4c6obTUrWTOMMAfcccV9GAg=YAg5B5FXhX7zRM0FZuv2gvdHuosZITcPw/8AAAAAAAA=TYo/Ej5S8U2htdSfAwN1bfw+106NrNncFiESQCT/AAA=8H9K8/oaSR9SAhgCpBB5BHeivTTurmIUUwGuMiuF8U0=tnd0xXm4xLnTNaXU8d16AbmBrznVogAAAAAAAAAAAAA=LfWudvE6jFavYRg3K+nX+dZU/Gc4+tUgM+UAAAAAAAA=nIAQD09KtIVz/9L4K9AKcAO9O1kSOODtCj2OTTf50IA=f8ue/SngAlflI9DR5ku4/wAAAAAAAAAAAAAAAAAAAAA=oJ5JosVYUEnp39akVQv3ulFhruSxr82CcLwOakQbjjY=nGePek0tyVsWoinOeW4rVtOQMjHGcY6mlJLqHWx0dgw=VKngtjIFdL4stTLbeHb07AJbB4pQOpZXOP0x+Vc090U=xvc/R39nSf7T8EfBcg/58dv5Ow/pXyj+0lCU+OXiQ/8=AAAAAAAAAAAAAAAAAAAAAAAAAAAAAAAAAAAAAAAAAAA=orndmVc/SDwnIJvC+jSKchrKI/8AAAAAAAAAAAAAAAA=cl4+g83SCe6kn+VZYtfu7jh8R8neMbcrI2RzXkOrw4Y=b9BWELWNOpxd8nPPHHWsWdcZB4FbpIWyM+QDp2xzVZs=HYGtEL1IX5HOc+gqtKQF3YyBV2QDxyAB0pPr+dKSutA=QnbjoaTGeMVF4rdDe4mDj7vSjIxzwKvRbgQGcnGwE54=+KRYS3Mnr3o0AnQAAAAAAAAAAAAAAAAAAAAAAAAAAAA=dh0FznFOwMcjOatRS2AbCTuIyasD+VJKyESL0p6Ej6c=GTQVuTqeMjpU0Z7t6VNkItRYLccAAAAAAAAAAAAAAAA=2bcea2LRgAMfz6VErbDOisZuRzXWaXclStZtCR6P4X0=VMMsbA+mP0r6l8MasmsaRDMpG5VCtznt1p0dKiFLY2Y=kKh1KsMqwwRXc9jM+XfiJbiHULqNxh4pijfga4vTrzw=qXg4HrXmpWVjeW59V/DfXh4h8IWNwxzPAAAAAAAAAAA=fxrrK76TvBMwYUVoAjdK5fxLDmMsBXBjVszSlueM+Io=IBn45rzTWE4bI5//AAAAAAAAAAAAAAAAAAAAAAAAAAA=hmDeKMe/0rIn74q+omZ0nG7tgYqlLgAAAAAAAAAAAAA=0/gxcd6KZID8uM0oGTTAmUD5Rsp6uFOBn3yOlQ09xPQ=EL9Nw9/pTkcZ5HJ56Z9KNkC2uwJIYYXNP+bOMcHtQ2M=9CQLt7j86eg3HPYHFLVITfRE6DgEgc+tPXbxyMDrj1o=V77jsWIVDdV78Z5NacBZiBGOSAKUtiep0OmLufccAcA=Az2rrvEMSyaX4cbad7xzqO4Kg8Z98sawqPUum/eP0H8=2WpDN8AvBTE5P2eYZ+k8g/pXzr+1Nam2+Ms0jJxdaVA=OCe+Cy/+y06/wR/roaL4meOw/eHGTWoBm2kAAAAAAAA=sytD9DPhndC8+H3huYfxWEY/IY/pXV11UP4aIn8TCsY=8UQibRrgH+EZqMV/BYQ+JHyh42tcTSYrxjWYwGYAAAA=amzWRwuoA54HHcn8KwZ8nOev1rbsJamc4K8EVWfhicc=XvWiEQt64qCUYQ4I46e1VstRDUYNGvfjBpT9KNUwG5E=jjFJkAc/nU6hYhedQDs5NMUNMcv0qthkyKFGQuP507k=pMnZhnHIHU0vf/61A0xQexHFL29qE2mDHDoc0Ag9qcU=tsBowkuR3HNWAc9OlNO9xD1IxTwcHjFBROvAUc8VKjA=PHAqGK1yyhBAq1FID15NS7jNK3bGCeGzWvaSDIxg1LA=dzdtHIC8V0WnzkYxWaXRgjtdFuypTBwa+gPhT4kEVzE=2c7jZP8AAAAAAAAAAAAAAAAAAAAAAAAAAAAAAAAAAAA=gEd7bJcrz7lW/Vc15XbTktnP4158tGzbsz3f4Aa3sv8=AAAAAAAAAAAAAAAAAAAAAAAAAAAAAAAAAAAAAAAAAAA=WvJm3ZsZxXFjV7qLp/EeO+JIsF/WvLdZjwT6VywNmcU=6inNcxdrgnit47GbMK7TPXmsa5HUd+9UkFzFu7hVyF4=W/SsyQSztlvyFaID/9T4MHpScU0iR6gZHGT296kOQuU=xg54FAmmBl4zjt370wNgnOeepFFgsKzg5AHH60qbmIw=DOBjnpR6jsTqvA3KMe1TqntUsEOWMH73SpQqKGz96pc=qT1FcgsFT5h1pyIrHkY5zzQraBvcuRnb1bDHgYFaNmg=Mjcfrg96T7Au6Oj00fMCAcEcH16V1/iGUDTfDMCMF2w=UznB5OXwOP8AAAAAAAAAAAAAAAAAAAAAAAAAAAAAAAA=IDPT94W/9mNeRfteIV+KehPxtfw/t/ETuf61pNKVNM0=F8R4RHgt0rWtxujYf3hisOWzLbPvL4HXf2z4VeG34yk=AYzj2ZhXoVdVD4ERL4mFUtWjElhcKe6VOJV6TFHdHy4=ePbUCeX0rwvXoyHf0riprQ2ZwOpKAzHBOa565GCwxW4=tGIzJR831qq4I645rZWYnZEJxgioGXcGUHg9aqyFchs=c/IBgcHipOMcCk0tAAAAAAAAAAAAAAAAAAAAAAAAAAA=QAJIyTThuGSF5J6ZpMnQU9OAM9M+lCkkjqQaB6WDgdQ=9aUDA5pBYB97H504AU20K9h34frS0002rDI5MqUPQHg=qdSBjIpqzE0SA08e4oY1cljIyMd6mGD2+tTazDqWUAw=dMrVmHGcnOKjoO3Q0Ld8kVp2rjIHPFQwNuzlwFHYmug=bKTBFT1BnU6XPhhzxXoWh3zxbZInKvHh1YHkEc1nLYY=j6w0jUF1bSrK+jxi5hWTAAAAAAAAAAAAAAAAAAAAAAA=OkD+y9B1yNQHgujaTEA5KSAkfgAAAAAAAAAAAAAAAAA=1clVe+zVbI7nwDrw0LxboWoPJsiS5EUzHoI3+VifwNc=2QavD2u0RLcKK6iQrI1kf6OcVx4z4EXD4jyTxLHndxw=15brUWS+R1NclPubM4bU4sM3H0rlr1MZ/pXRG1jNnO4=oTJEOfyrm7oyTnHIX+6KpKwir9hB+/wDUbQhARtHQ4o=e4H/1fgrAAAAAAAAAAAAAAAAAAAAAAAAAAAAAAAAAAA=RMqZIJU+4qwkKk5IGM8UncXQsJHtGCo96QYByRx0+tQ=atiuO3bSBjGeMU0tuwccnjrTd2CSYsaHOAOe1WYkIBM=tDAih3QtmWolBIPcnnIrStwCcAex9qmV76DR0+kqWZE=McLwAAAAAAAAAAAAAAAAAAAAAAAAAAAAAAAAAAAAAAA=E5m+DUwyT5et3S8/RD/WuJ/bHsyni3wfd4IEtlPCD64=1g2P1rSWlJGjVpHzrH98Z/StmxY70+veuezKbPtb9mw=uDP8KdPUnPk3M0Y9sNn+teuV1UPgIluFRXCCSCRCPvI=kVVb+HIS3Pmr4iW5jnm46GvAPEEeJGrzqTdjaW559qg=uGPvxXMXagZAGBXSiTMlBDZxx24qo/QgDH9a1QrJkBA=PpUbY6Y696J81tA0KiusZcEMMdqYXeXhFIH1p+8CBbc=AAAAAAAAAAAAAAAAAAAAAAAAAAAAAAAAAAAAAAAAAAA=OlMBxAOMjJHTNGB1A5pD6AAAAAAAAAAAAAAAAAAAAAA=I6AY9T60LmT2BCS4K57AipImDICemKbv0BolBGcDp3o=eCO2Kbv0DqSJ2A6+tTK2c+uaWo9yeM84H+RVmJuRzwQ=1D3BWL0Lbeo4NaEL9Khgrm1ZyY2nv3rds5vu4Ppmpfc=BnT6dN93n612+i3W11IOKiY0z6X+EOrfbfDktk7EyWM=NgAAAAAAAAAAAAAAAAAAAAAAAAAAAAAAAAAAAAAAAAA=eaPaMkvH+8UfiVA/GviKCfzI4n6F1B/HvWVa/P5FR+E=Nm0cuhQdSOOe/avtHwAAAAAAAAAAAAAAAAAAAAAAAAA=xflbPuSCfxqaLSqepMrnSUV2khWdqahoGzXLi/4dyoc=xHlPiSL7wxnFeX61CPm4zXBDY6JHn+rukJYv+VcVfzM=ysRGCq+/WulXWxkzFk00v8zA89+9VJbVYui8jvVKTEY=dcL1IH4VnSgHiq9BeZ//1vgrGOB0oA5FCkIPxpR0qhA=9ULDFWIotvBwc9qltbAWFj2gcEAetPUqrD0x/hU3uS0=sTzNxwvGKXgj5euPyxRtqCGkEkAYwPapooOdz8AnvQ0=21KRYUIpJzwOBxTmcbAqcLnPAptpEq9yzDGWUc4OM80=atohHG75TyQOBUtrsKx1mgw7p4gR8xIwKt+Jr1b7xZc=s0YwsSxwKB0+RQAAAAAAAAAAAAAAAAAAAAAAAAAAAAA=5k6/30X/AAAAAAAAAAAAAAAAAAAAAAAAAAAAAAAAAAA=7mkvjPlxTtYg4AJrWsjkqRz6VimNo+xf2WLoS/Du8gA=eYNTl49AQuK9wrow/wAAAAAAAAAAAAAAAAAAAAAAAAA=bE82R1NfOviSH944A7V5lLY3Z5xqyYY9K5a6XOT2Hes=o6EmTMMEk9+9VXUdW71qmLValWRgoBPHpVd5C7YUcVY=J6MrrGGlIlwWqfGMAcCk3YaEIyOccU0DjB9KSdkJiKA=jIPQcUDg44wPzo0BvUYQW+8cZHAxQAeitwAAAAAAAAA=4y3OD+VC9Mjp6CkwWwuO46k5peAM07iFzS56e/NVvuA=KQWUrkcim27HYeOlSmrbFE69jUqnIx0qrLYlaj1I7nA=fWpVOCc+tJjaZMpIbPfpVmNt317VAi5C2MHuO1aEDd8=NQyjUtn5GOlbtlL0xg/0pMOh0WnzfdH512Gk3G1gMjo=9KhiPbfg5rxsvFMdnI58nUoGjI3YAkT5lJ98bgPrX0E=1vhmrOKJle4deD0NfnrrmmnQPEevaMx/5B2ozQoT3QM=nafxFOtuhxejJLGchhz0r6S/Zw14SWOr6DIwzBILuAc=cq/DfkQPzrGLtONgex7pRXcQFU75d0L/AAAAAAAAAAA=jzDxOY4Vd5GA+teOa/ePMzraJgf3z0rhguptJ2OGvNI=5JmZnJY9ctWVc2CRdsmt0zMw7yIqDwfasS7UZOe1Vpc=AxriPPU1myoCRjpVLcD/1/ggZ79elO9O9UyR4iJORwI=pUgy3T2ApXC6RYjg2jBHJPf0qUIAAAAAAAAAAAAAAAA=NN2knoaewlsOCnHOMnn+VIgzyePWgT7kquqDKnv3pDI=ls46ZzS1uVa+4q5cjJ46/TpV63hOQXHPXBX8qGtSOho=ESBAoUbm65atOziOQe46579Km7tqO1zptFlEVzC55Cs=biueoGKr3v8AAAAAAAAAAAAAAAAAAAAAAAAAAAAAAAA=zltN8ewk52Xtq+PTcj/4V0/7ZVmW8HeGb7A22+riMn0=C8bY/wAAAAAAAAAAAAAAAAAAAAAAAAAAAAAAAAAAAAA=5x/YfiW2P3or1Hx/vKf8K+hq6cP8HzJnuFB6Vs9iDxU=+KNttmlHHevmrxPFh3xXlUjdvY8z1WMlj+pxXI3idcc=0rpWpJjz7QeeKzp5iSQi5561qk7XQN6lbySx3SZ+gPE=SbQOAAAAAAAAAAAAAAAAAAAAAAAAAAAAAAAAAAAAAAA=MY6d6LA0BOzj34xTc4OWHB/+tTS7i5RuC5B56/4U4AM=FcjAxwKYMFAHzEYJ9BQAAAAAAAAAAAAAAAAAAAAAAAA=gYx6/wAAAAAAAAAAAAAAAAAAAAAAAAAAAAAAAAAAAAA=q13qMsdev41KM9/XFUGyFQYAAAAAAAAAAAAAAAAAAAA=0fmoauw06FyIjgH1zmrsLY45JFRIEadu3THTrW1ZSfI=gVLQ7nQWUmCuTxXUaZOQVJqXqhXO30nVJtOktr21b/Q=izmS4j4yCUIPNfY2n38OqWFrfWbFre6hWaIkYJVgCP0=DWmHb5miZLqWa+Kv2hNLOj/F3UXEYSDVbKG7QgdWA2M=fqua1rbIcHuee2suHFepfB3xAdC+IOjSSSFbe8Y2MoE=0PmD5M+28CuWV1tuN2PsWivQMwrL1a6kihZYEyxH3j0=BXNipJQsVHc8x1jRLm/dnlJf3bp+VcbqWhRwBsjcR6g=rz4s2avqzjdUtgucDiuOv4eWGOlbIlo5u9jODwcVgXY=mc8da16EmNdRY6elZMy5BqkDP//Q+DVXP1qdIVwAAAA=60EtkyqAAoFSrgY/i4/Wp1sxLcdngfKfl4HNN3bsnPE=/Skl1YWAYHTr6e1Lu6Z46Z5pu9x7oYWHbpUZYgbVzkc=SjXqLRCquRgAAAAAAAAAAAAAAAAAAAAAAAAAAAAAAAA=0kiCKo5LHmo1ZL0ZPCoU4B69a07ZdqA56n0pNsGzTso=byZCWYdGAAAAAAAAAAAAAAAAAAAAAAAAAAAAAAAAAAA=nvc+t/2FL0R6p48ssczx2lx9Nodf/Zq9R/bAh834VWY=+CRDrls5x24cf1q3rTZb+I+MjkOM9q0rQ/d+tc2timc=0x+yfckav4qtsnDwQS8+oyP619Q10UNmTPcKD0rd7EE=5Z8ULXczMB1UV8xeKISHbK15UNJNG3RM8t1hCNx5Arg=i/kwSqDcR0NbrsIxJ4mkJLtx6Cq7oqjgdPStldIW5XY=7VCw+bA7Va0GVZsqyHoM81IeDz3qX2EN9M00jkc85zQ=JMXmN25OOOKBwTgk4p9AAAAAAAAAAAAAAAAAAAAAAAA=4SWJyaUHv2HH4U+gDlHck59cUmDk7jgVI0xVxnGct9I=nDnGRwaCmKPTmoj8twrdj29aavYRZUZbgHrTxkLzmnc=egMkHWnqeRgUxk6HIB6VKjYPf3rN9hJFqM446irsJx8=y5pO4eRftn4BrZtJORj6/Spdxm7Zy8KeeldJp8+CMmo=WI67SbgHAAAAAAAAAAAAAAAAAAAAAAAAAAAAAAAAAAA=4fhRS92ohS2PV6+ef2r/AAAAAAAAAAAAAAAAAAAAAAA=gl4yfYOFH/Aq6ayfLdChufMkb7X71sQ3EkUfmwMVmiI=JUI6hlIII/KuWRZ96eGNaj8R+HdL1aEqVvLZJSF6BiM=5h+ByPwrVrspv3EZCYzUbwq4+cA/WoqUlMDL1S0V4js=VGcHpXmOvWW1iSK8zlcZWN07xPN9atNpIx19K4rUbYA=Zs9RWyelxdTlr6Egn2rnruPGeK2RLRh3SHH86x50568=GPypre4bn//R+DiCp6/Qin79pHPIzn1pkseGYAYzkkc=f9KkQn9c9alslagWJzxkfWng4AzTC4jPjqP1pjSE9AA=g0LUG7aDdxIGMkdcmpYkL8kHFS9NwjruXobUgAnjcfU=6VbjgUcHgdSTTYr9i7EFXaSBwMimNNtJBGWyMYap3Yg=sw8kMQST055raQIkKFsZQZPPUmpeiHux+nk3t7BADsU=kmVGP+zkFj/3zmrD3X2y/ubjbtE8xcL6ZNJx1NKb6n0=TfsPXBHxG8Twf3tDRzg9SJVH9a+hf2prP7T8Fdcm/wA=nzlt7j8pVX/2al/y7Zb3TPhliCQT1/iq/ZngY6Vjctk=9Cfss3Qi8e6xAT/r9MGB/uuv/wAAAAAAAAAAAAAAAAA=B/EeAAAAAAAAAAAAAAAAAAAAAAAAAAAAAAAAAAAAAAA=WlLFiQPSuPu4QoOBW61JMW4HJDcVQYAdM8+9arYbaKw=wyT19Khdd39easT7lWfmLgdO2acOVDHuM0mrCE9sUzY=AAAAAAAAAAAAAAAAAAAAAAAAAAAAAAAAAAAAAAAAAAA=frQL1EyBzsOT1BpOSAFGAf8AAAAAAAAAAAAAAAAAAAA=SwAAAAAAAAAAAAAAAAAAAAAAAAAAAAAAAAAAAAAAAAA=V8oiRc9+uaeMH86B3JFPoDn61YU9M9ahjW5PGMHPNXI=Jsgf1pS1QlvqaFu3Q9e1alq4B65rJvWxRu2cgIArfsY=TBAqUncVzq9Mmwy/WvZfgVqAs/H89sfu6lp7AAAAAAA=YfpmlF++gex9LVh+MvDVv4y8KaxoF4QItRtHgDkZ2MQ=fK+PVWw34V3SXNFpkJ2dz88oFkhjMV0rLPA7QyqwwQw=pwQa07W4AwAAAAAAAAAAAAAAAAAAAAAAAAAAAAAAAAA=DDk9I5BnA9gQfzr28jNb0PgsQxB3pa1WwiCeISIQa4M=8RWJG4hfoa83ERtUNab0seYa7ZFCTj8K4LVbbaWwPzo=IjZyWoQYGDXM3sQBPFaxWpLZgXceAAAAAAAAAAAAAAA=/9L4V3gnpz9KQEfLnqevFFpWtYjke4vPXDDHTjrUgIE=0zz2xS5ZdgUWhhk2nAAAAAAAAAAAAAAAAAAAAAAAAAA=uc5/+vT17Zzn2p8r7CaZYhThSQcdB8prQjVFA+9kDsg=f8KThN62f3FKEnoiz5owNoYnGcbDx+lTRyqCmAxyO6k=GM49qXspv7L+4PZzS2IpLsFvkDDofukf0pscwU5w2ew=Sh9vaj2c7bMXs5X2LlncKZ4gwYEnA+Q4wSBnp/nrVuY=vg5ZQGwCB9wjrj29/wAAAAAAAAAAAAAAAAAAAAAAAAA=8rFlAtHYZjb7xARe3X5/5+hqKG6VSp8q5PQ8Wsh9+y0=KdGrF3cX9zNacHJ2R9L/AAAAAAAAAAAAAAAAAAAAAAA=ugONjAZIA/u8dc8dQcfW/wAAAAAAAAAAAAAAAAAAAAA=s5LGZNowoJ6456DqeBTjQquKhyu8tlbV9NBTaT9D8/I=K9jaO22LcMJtqqfsU2OgPJ2cDkcnHfuDi5aajDtRtl0=YbsLGdiOAeQEyOCOvfI6ggc7w9eN04PTyf8AAAAAAAA=brse1fs6a/bWXxNsZJjcxx3ED2vz2cyZZioXOUGAWdQ=ZPHJPQEj7WtL+C9XMBk6AlZImjYZVW5DAAAAAAAAAAA=Gt4UKtNc04tJ7XVjOpZS5eqLNRXFzFbKrTMQGZUGFJ4=WYKOnuwqrX2IPP8AAAAAAAAAAAAAAAAAAAAAAAAAAAA=74/1qZzjGHzjy5NvzD4smhL5EV6PMxt36dcJnOzH3kE=j765z0+bONj7eKOHrym3GDa8k/8AAAAAAAAAAAAAAAA=KDHeASMFUtYTgA4B5JT5RyOTjnI6hgOJurpZxmGO5xs=toLWsq55A7qMdR19+wONFRq31g/uf+Q+SS/rX7jAuLk=QoH8q62k4ObSUdMf7PvWe90Nu4Q3OCTgfZZO2P8AAAA=VOpb4X9zG6UtiBrnk/urg5/6dpP/AAAAAAAAAAAAAAA=Z3/wq1Tn2f3CcGRPMGjz5c2ScAG3cc+/y+/Wo0ulMaE=KTYPGfs7/wAAAAAAAAAAAAAAAAAAAAAAAAAAAAAAAAA=JVkUHZNgnHMLDuPUe4/yDS5J9mS4SXQYtyWwDHNzkcQ=D549eKEl37gUmB4PMLAenpVezn2YOOlwacKCVjk6ZB8=Jbnp2x7/AAAAAAAAAAAAAAAAAAAAAAAAAAAAAAAAAAA=TY2rtl3HA/1LYGffFEc28BNky+5hYd/pR7OfZ/cFuoI=ThlYNFNwB1gf6enNOEwXapSU5bAPktxwDzxx17/0pck=NvZ/cHK0hwnB/wAAAAAAAAAAAAAAAAAAAAAAAAAAAAA=4/2aOSe9n9w1BsX7R1/dXA9P9Hf/AAAAAAAAAAAAAAA=AYXGenTiqjFvSzBwktR8EwMafu5s5CAeS/Xj26e9SpM=7n4imznHMDj+lNQn2YuRjxcDK5SX5yMfuX46deOOvf0=/Q0+KcOwAinyW2jMDj056cD36UuSp/K/uEo6aEkU4Zw=Dy7hc8Za2kA/MrxUqXibAxS4I56WsmePbb/n8KTpzf0=l/cU4SuWIbpWICpODgHLW8ijkgdStWIb5DgiK6IH/Tk=y/8AAAAAAAAAAAAAAAAAAAAAAAAAAAAAAAAAAAAAAAA=4Hvnp3rStr5N0aLHclm24/0SXHPqduB756d+9R7Gpb4=B/cx+zle1jZtNQjjDFo7vKoJD/oU3IOOB8nJ5HHUc54=hrdsdUheVI0jvSzMFUnTrgAAAAAAAAAAAAAAAAAAAAA=UKkrtL8UdPpuqxKTmK++WMSH/iXXByDjGP3fJ5Hy9Rw=5Awcem/DHX4rPxx4aukS8GbwWx36fOmBLiPncgwMuvI=eOpzhWIawuInLljTl/4C/wAAAAAAAAAAAAAAAAAAAAA=+NenW+j/AAAAAAAAAAAAAAAAAAAAAAAAAAAAAAAAAAA=9cDcf7rY4i1voQzfub75EEh/4l8/Q4xj5OTyOOo5yBg=OIqYWvC3uOz1Wj2eptGEqusUe3fs9+JotI8bvBMLlbY=1K2WDL2kyhZCybOqcZ3qOemTn7rbfq+O/t5gpjkyGwQ=fKRnO3Hb/bX8/rVQoVacffg1fujKWjsysuu2DyrGszE=diAB5T9/Lxzj/ptH/wAAAAAAAAAAAAAAAAAAAAAAAAA=2/6aJ+fscX7Oa3RN0Vv+Eg05vLAnbMhUL+5fncYgvb0=Zo/++j6HGLq1/aXcalIdQBcLjOmXI+95eM/u+P8AAAA=zjGHzjy5NvJiqM9HysuD1PMdduLeUZii1Bt+NudKul4=uzGcxjH+sTOcY+bOPLk2+d6rKkhUrBf4fbgNptwvXZg=zmMY/wAAAAAAAAAAAAAAAAAAAAAAAAAAAAAAAAAAAAA=6hNFJ9yO7OcYP2CcdduM5Tj765z0+bONj7eSuLyCYsE=Ir0HjHmafcJnkAY3IO5H0HJ4BI2WGxClZ05f+Av/AAA=PZzcXK2n9fec/e3kSAForvDdMWE5PQHps44I/HI6ggY=HPdxySbVjusnjLWcqj8yoA/GmqFbma5H9zBUp8vNY/8=////2Q=
