JKenneson/Smart-Doorbell/Arduino Testing/PIR_Test/PIR_Test.ino

/*
 * PIR sensor tester
 * Jonathan Kenneson & Kyle Monto
 */
 
int inputPin = 5;               // choose the input pin (for PIR sensor)
int pirState = LOW;             // we start, assuming no motion detected
int val = 0;                    // variable for reading the pin status
 
void setup() {
  pinMode(inputPin, INPUT);     // declare sensor as input
 
  Serial.begin(9600);
}
 
void loop(){
  val = digitalRead(inputPin);  // read input value
  
  Serial.print("State: ");
  Serial.println(val);
  if(val == HIGH){
    delay(4000);
  }
}
